kckanav/head-camera-cv/outputs/25th April 2026 - cam1 first minute sample 20s both hands.jpg

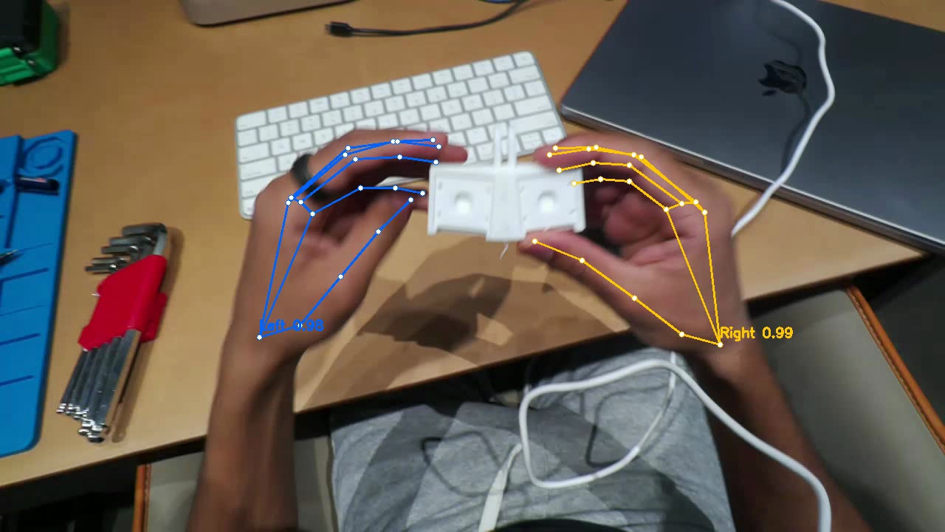
outputs/25th April 2026 - cam1 first minute sample 20s both hands.jpg
