kckanav/head-camera-cv/outputs/25th April 2026 - cam1 hands sample frame.jpg

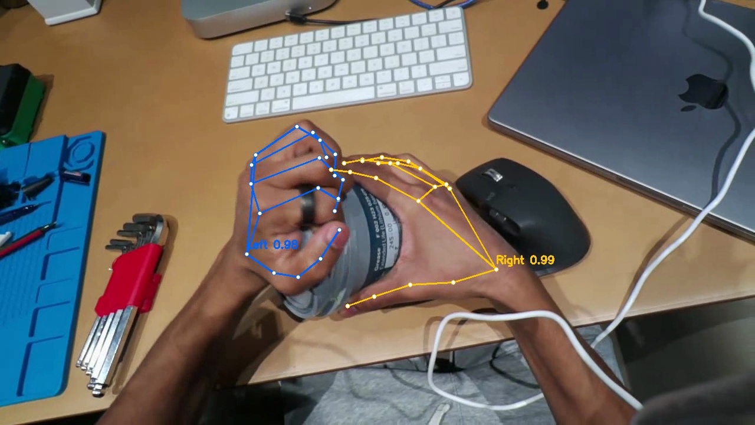
outputs/25th April 2026 - cam1 hands sample frame.jpg
