kckanav/head-camera-cv/outputs/25th April 2026 - stitched panorama sample.jpg

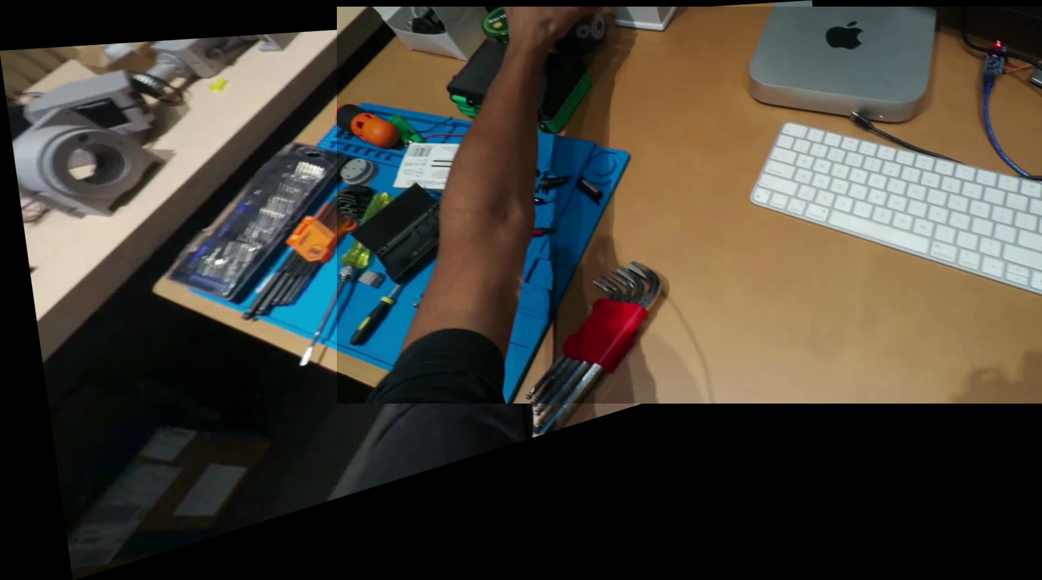
outputs/25th April 2026 - stitched panorama sample.jpg
