kckanav/head-camera-cv/outputs/27th April 2026 - rectified pair sanity.jpg

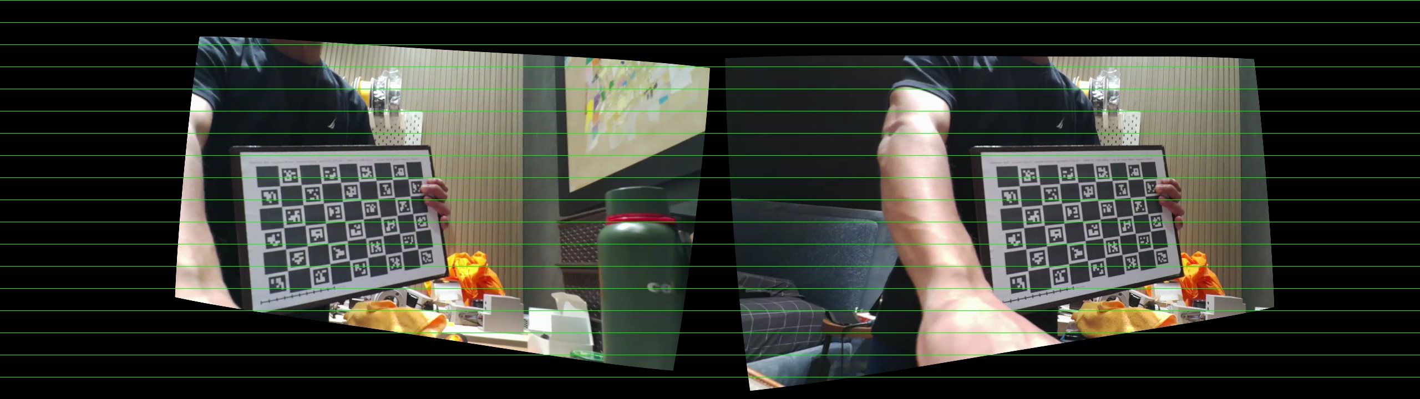
outputs/27th April 2026 - rectified pair sanity.jpg
