kckanav/head-camera-cv/outputs/27th April 2026 - stereo hand 3d trajectory.png

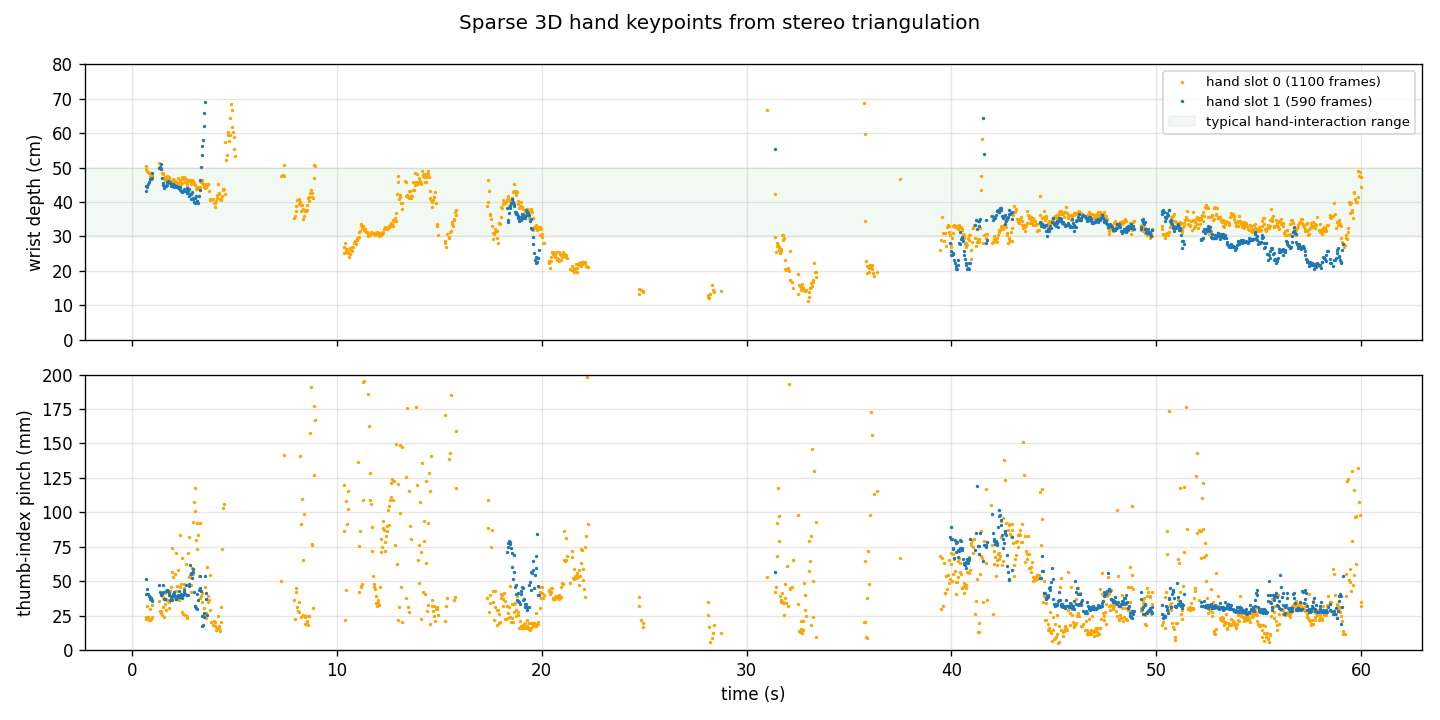
outputs/27th April 2026 - stereo hand 3d trajectory.png
