kckanav/head-camera-cv/outputs/27th April 2026 - wilor 60s perf trace.png

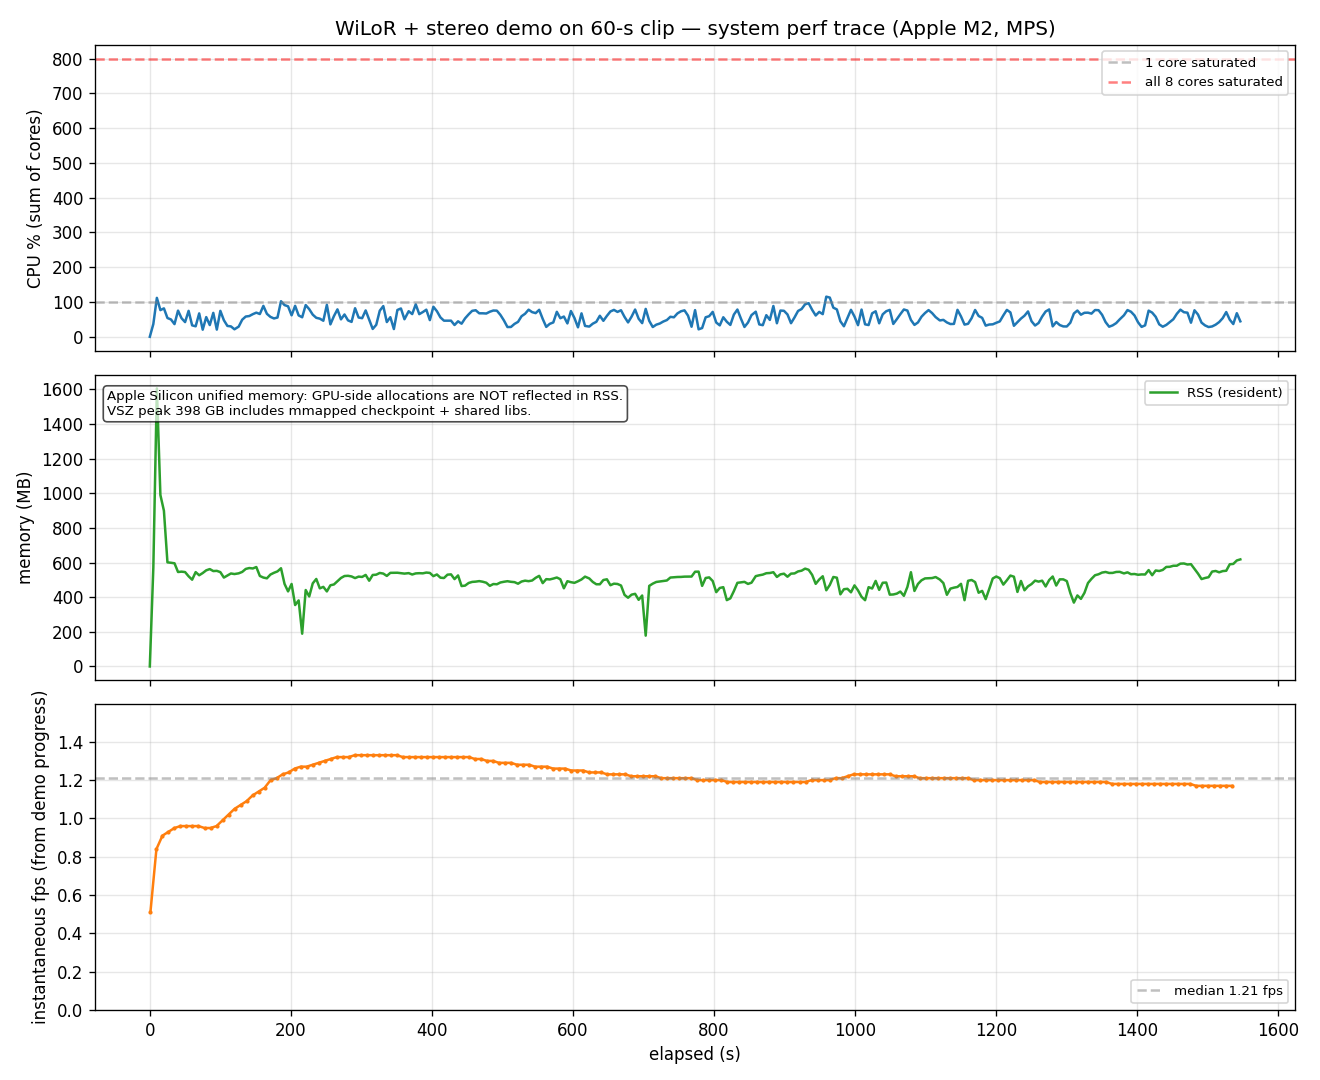
outputs/27th April 2026 - wilor 60s perf trace.png
