kckanav/head-camera-cv/outputs/27th April 2026 wide - rectified pair sanity.jpg

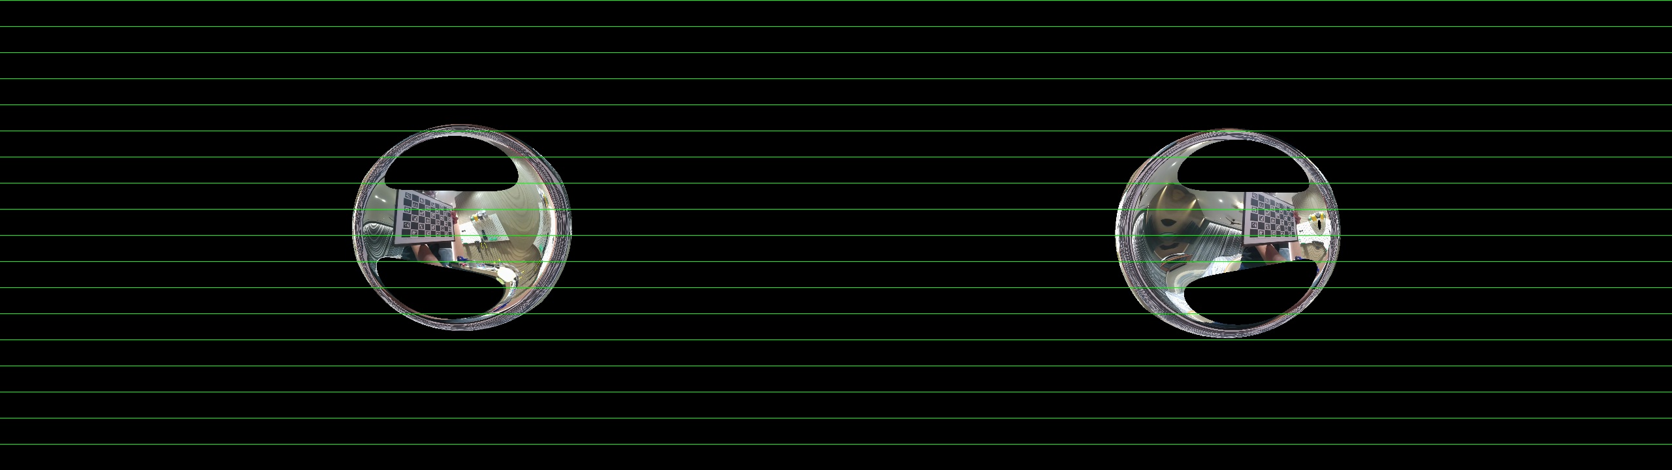
outputs/27th April 2026 wide - rectified pair sanity.jpg
