kckanav/head-camera-cv/outputs/30th April 2026 - phase4 inspection [20260430 manipulation].png

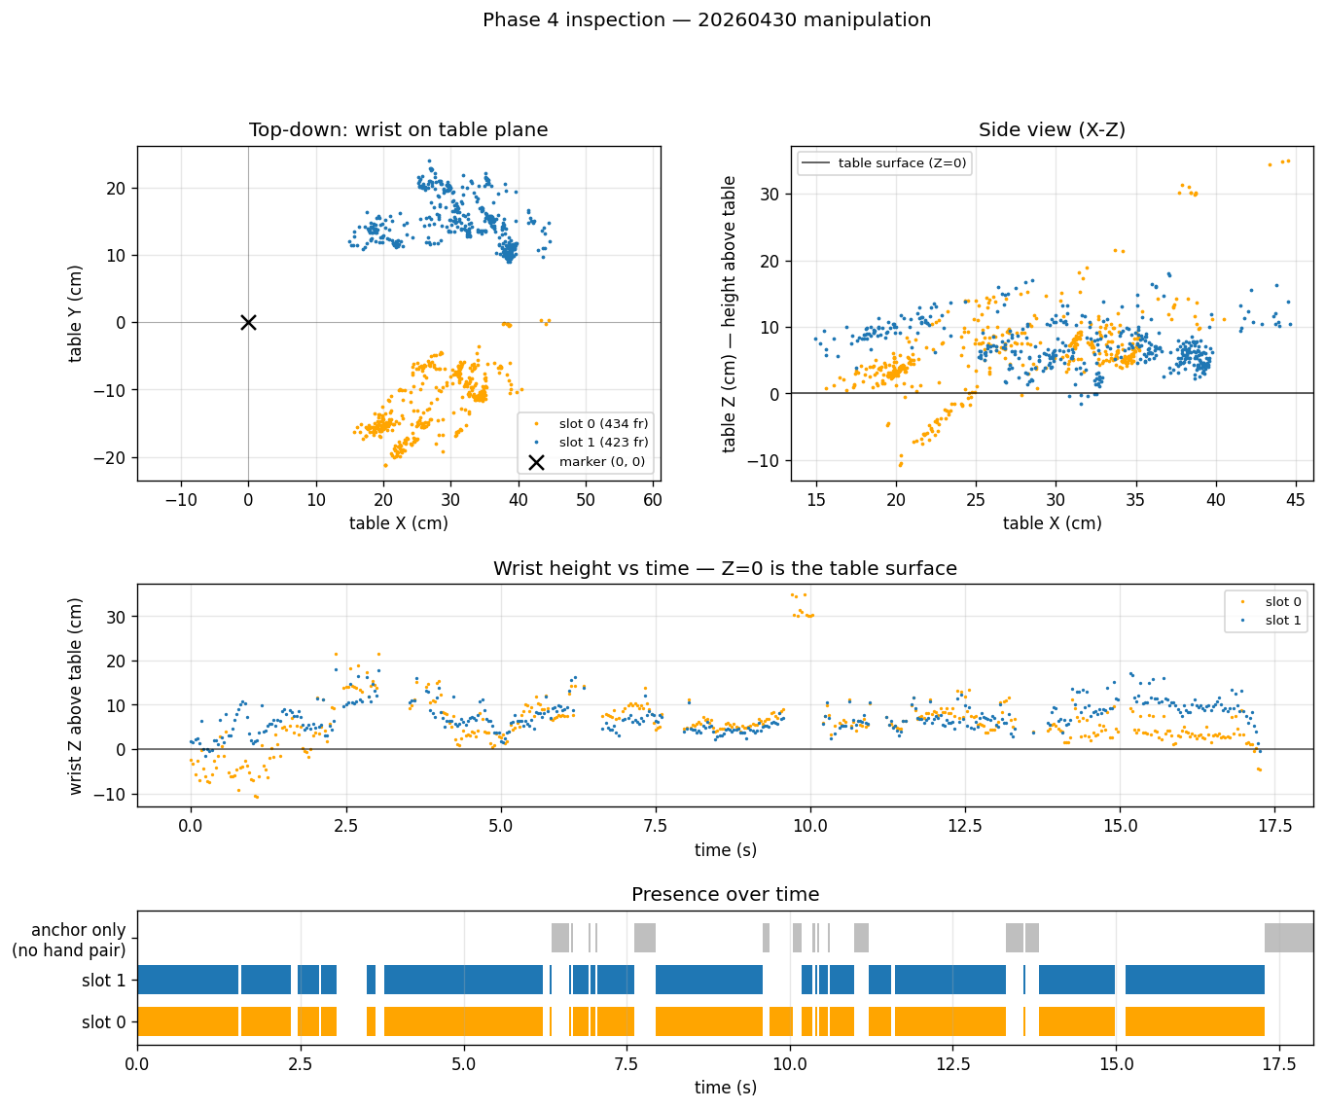
outputs/30th April 2026 - phase4 inspection [20260430 manipulation].png
