kckanav/head-camera-cv/outputs/30th April 2026 - phase4 inspection [20260430 protocol-A].png

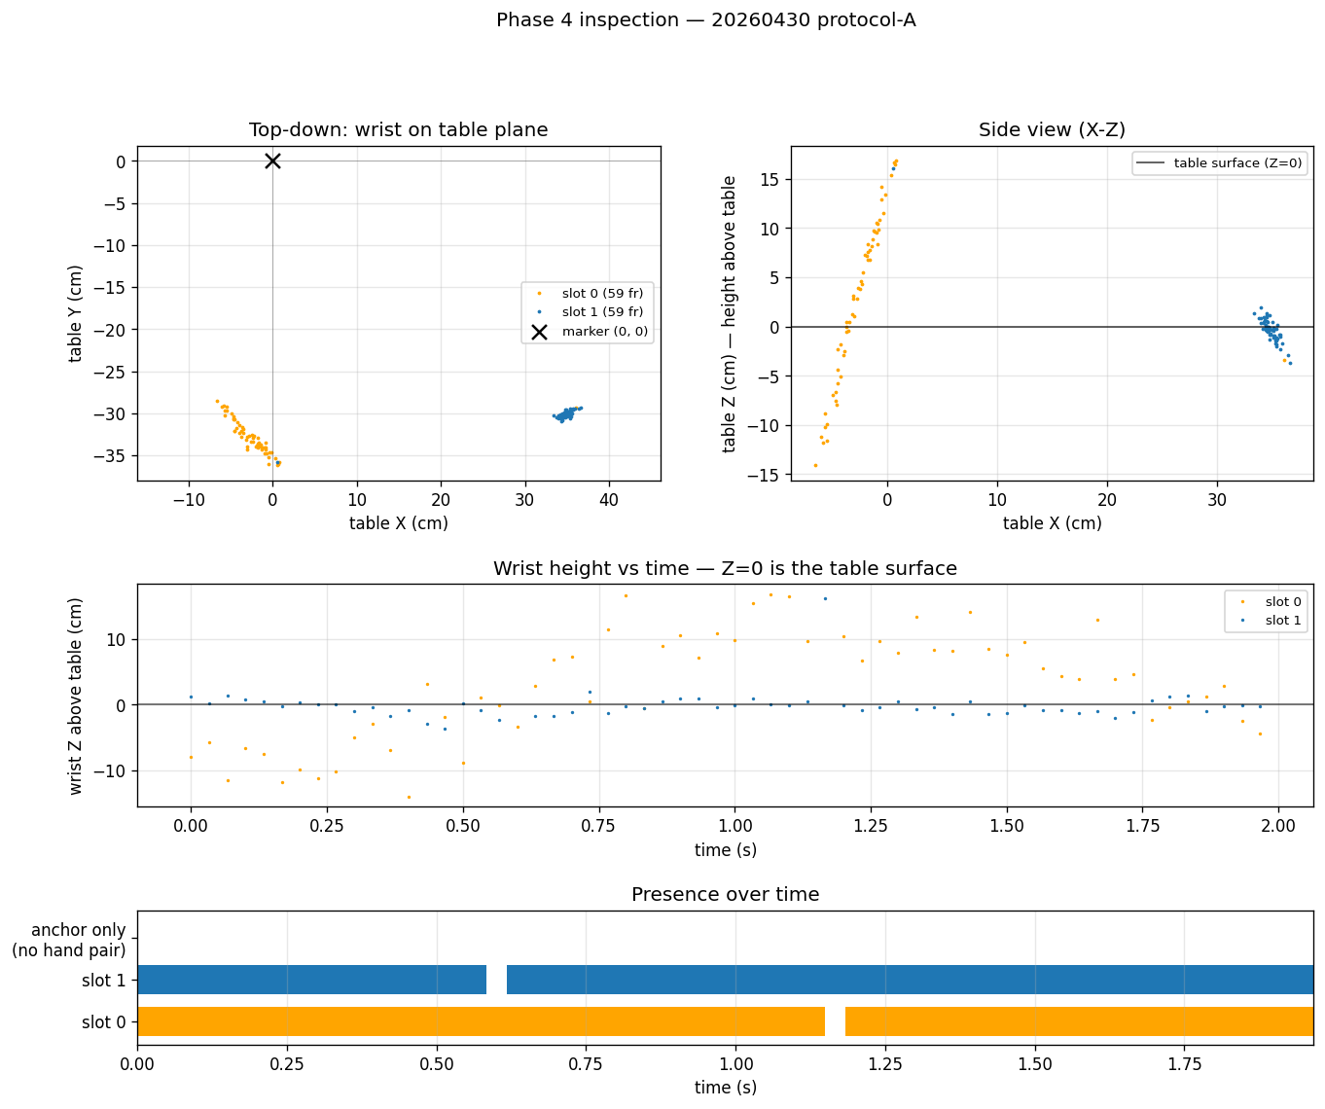
outputs/30th April 2026 - phase4 inspection [20260430 protocol-A].png
