kckanav/head-camera-cv/outputs/30th April 2026 wide - rectified pair sanity.jpg

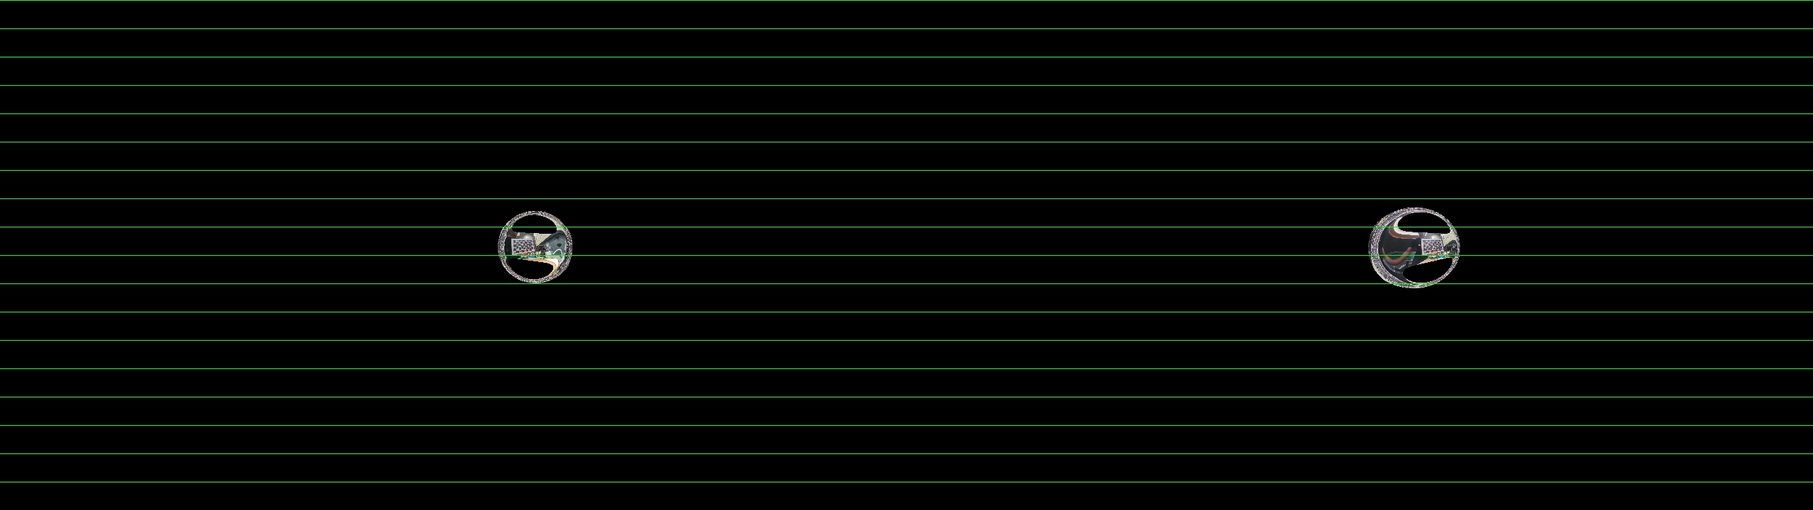
outputs/30th April 2026 wide - rectified pair sanity.jpg
