kckanav/head-camera-cv/outputs/30th April 2026 - mesh sequence [20260430 manipulation]/mesh_0003.obj

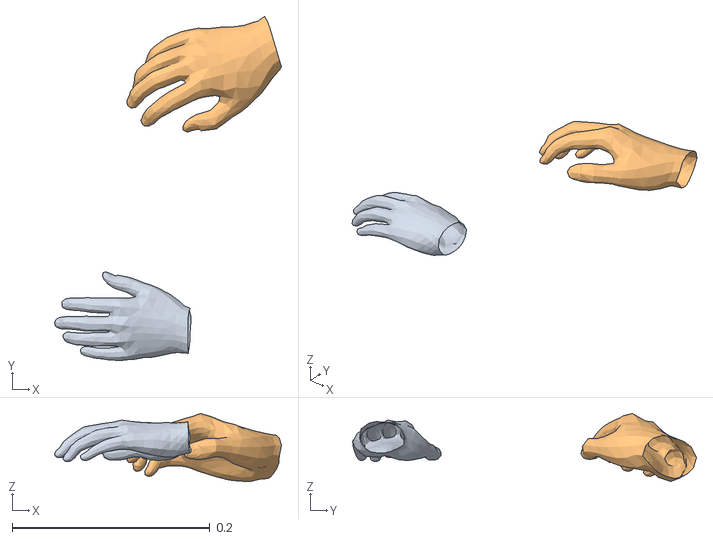
[picture p33: CAD file, 2026-04-30]
outputs/30th April 2026 - mesh sequence [20260430 manipulation]/mesh_0003.obj
0.229 x 0.348 x 0.0687
hand_slot0
hand_slot1
