kckanav/head-camera-cv/outputs/30th April 2026 - mesh sequence [20260430 manipulation]/mesh_0487.obj

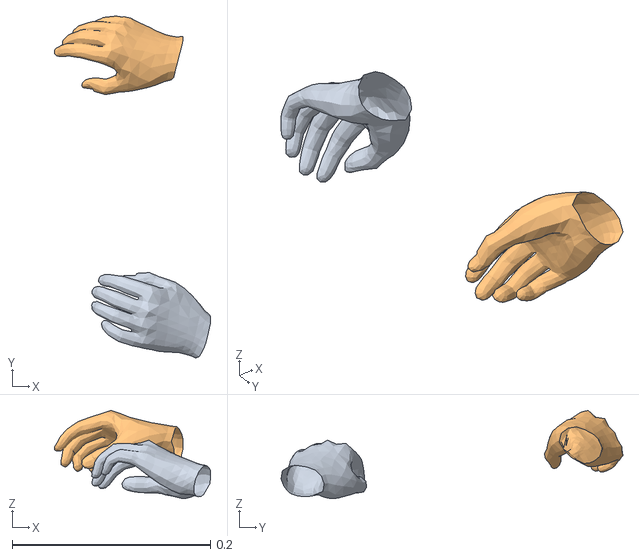
[picture p34: CAD file, 2026-04-30]
outputs/30th April 2026 - mesh sequence [20260430 manipulation]/mesh_0487.obj
0.158 x 0.345 x 0.089
hand_slot0
hand_slot1
