kckanav/head-camera-cv/outputs/30th April 2026 - mesh sequence [20260430 manipulation]/mesh_0384.obj

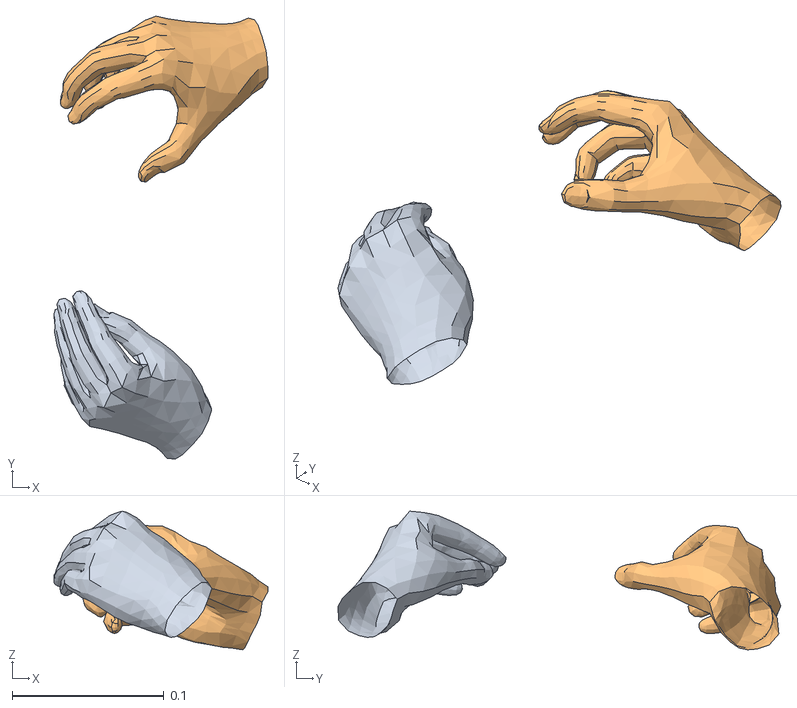
[picture p35: CAD file, 2026-04-30]
outputs/30th April 2026 - mesh sequence [20260430 manipulation]/mesh_0384.obj
0.141 x 0.292 x 0.0914
hand_slot0
hand_slot1
