kckanav/head-camera-cv/outputs/30th April 2026 - mesh sequence [20260430 manipulation]/mesh_0015.obj

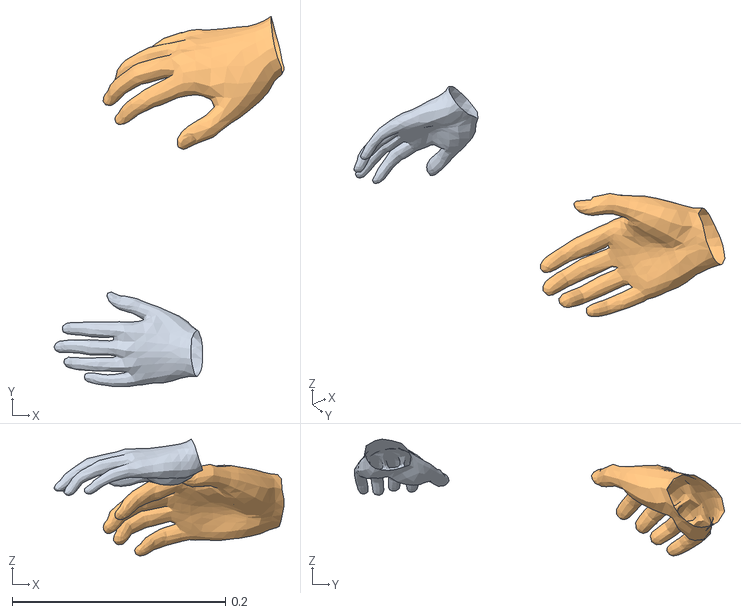
[picture p36: CAD file, 2026-04-30]
outputs/30th April 2026 - mesh sequence [20260430 manipulation]/mesh_0015.obj
0.216 x 0.347 x 0.109
hand_slot0
hand_slot1
