kckanav/head-camera-cv/outputs/30th April 2026 - mesh sequence [20260430 manipulation]/mesh_0325.obj

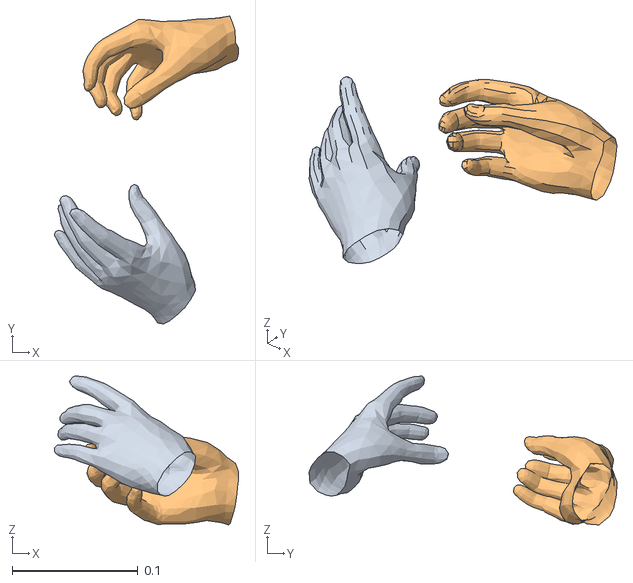
[picture p37: CAD file, 2026-04-30]
outputs/30th April 2026 - mesh sequence [20260430 manipulation]/mesh_0325.obj
0.146 x 0.245 x 0.118
hand_slot0
hand_slot1
