kckanav/head-camera-cv/outputs/30th April 2026 - mesh sequence [20260430 manipulation]/mesh_0473.obj

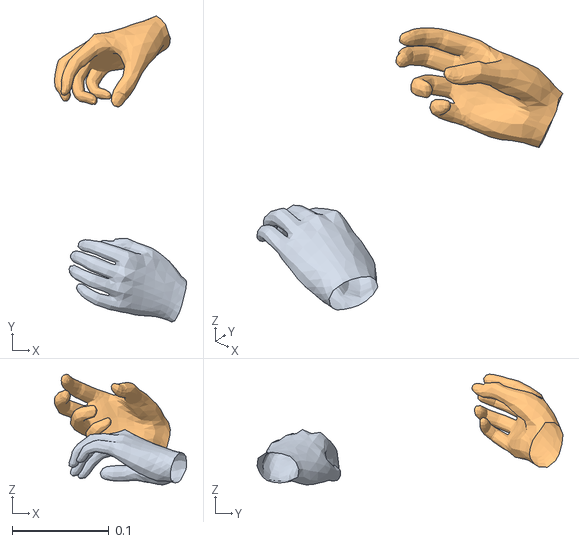
[picture p38: CAD file, 2026-04-30]
outputs/30th April 2026 - mesh sequence [20260430 manipulation]/mesh_0473.obj
0.136 x 0.316 x 0.114
hand_slot0
hand_slot1
