kckanav/head-camera-cv/outputs/30th April 2026 - mesh sequence [20260430 manipulation]/mesh_0043.obj

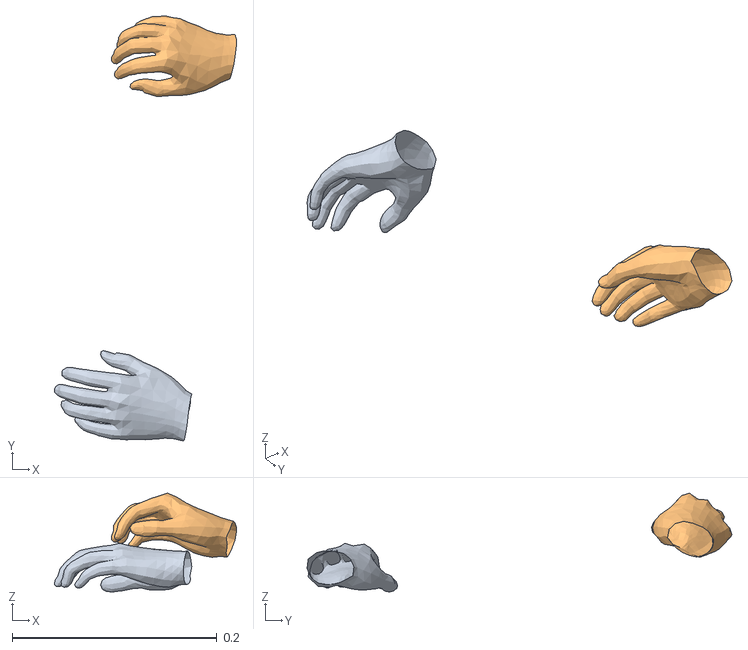
[picture p39: CAD file, 2026-04-30]
outputs/30th April 2026 - mesh sequence [20260430 manipulation]/mesh_0043.obj
0.178 x 0.415 x 0.0965
hand_slot0
hand_slot1
