kckanav/head-camera-cv/outputs/30th April 2026 - mesh sequence [20260430 manipulation]/scene.obj

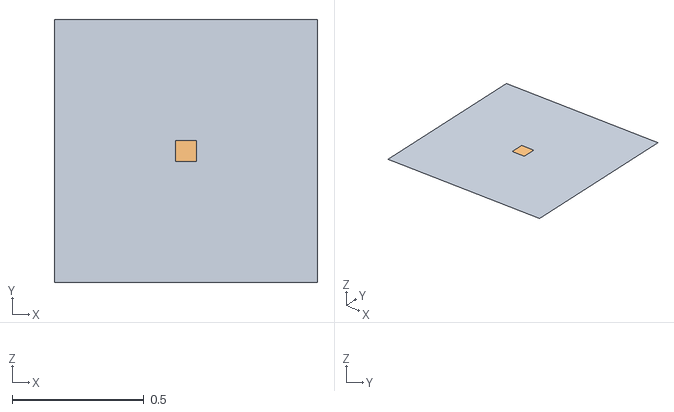
[picture p40: CAD file, 2026-04-30]
outputs/30th April 2026 - mesh sequence [20260430 manipulation]/scene.obj
1.00 x 1.00 x 0.001
table_plane
marker_outline
