kckanav/head-camera-cv/outputs/30th April 2026 - mesh sequence [20260430 manipulation]/mesh_0051.obj

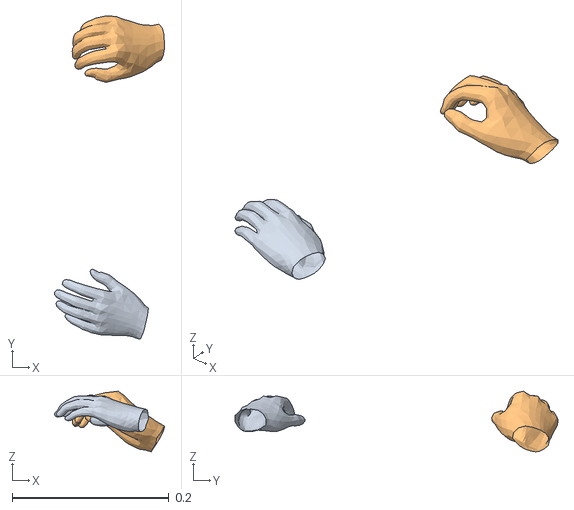
[picture p41: CAD file, 2026-04-30]
outputs/30th April 2026 - mesh sequence [20260430 manipulation]/mesh_0051.obj
0.14 x 0.413 x 0.0776
hand_slot0
hand_slot1
