kckanav/head-camera-cv/outputs/30th April 2026 - mesh sequence [20260430 manipulation]/mesh_0455.obj

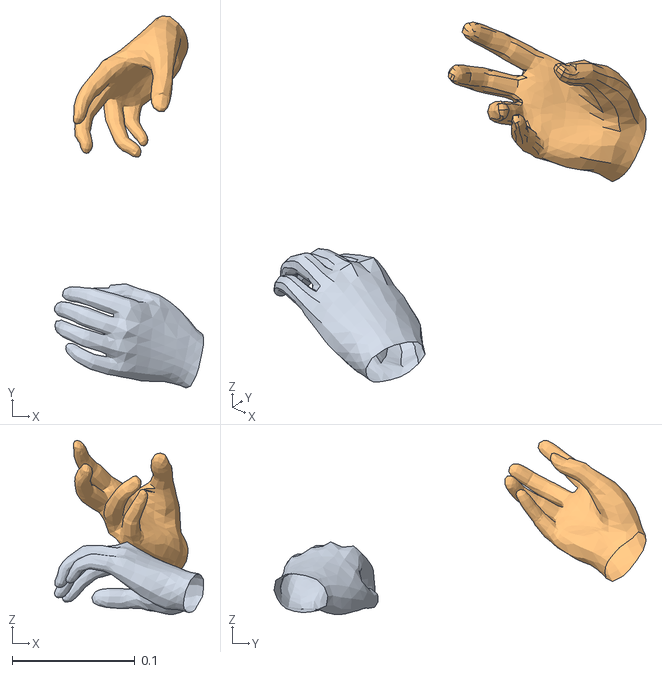
[picture p42: CAD file, 2026-04-30]
outputs/30th April 2026 - mesh sequence [20260430 manipulation]/mesh_0455.obj
0.122 x 0.303 x 0.142
hand_slot0
hand_slot1
