kckanav/head-camera-cv/outputs/30th April 2026 - mesh sequence [20260430 manipulation]/mesh_0090.obj

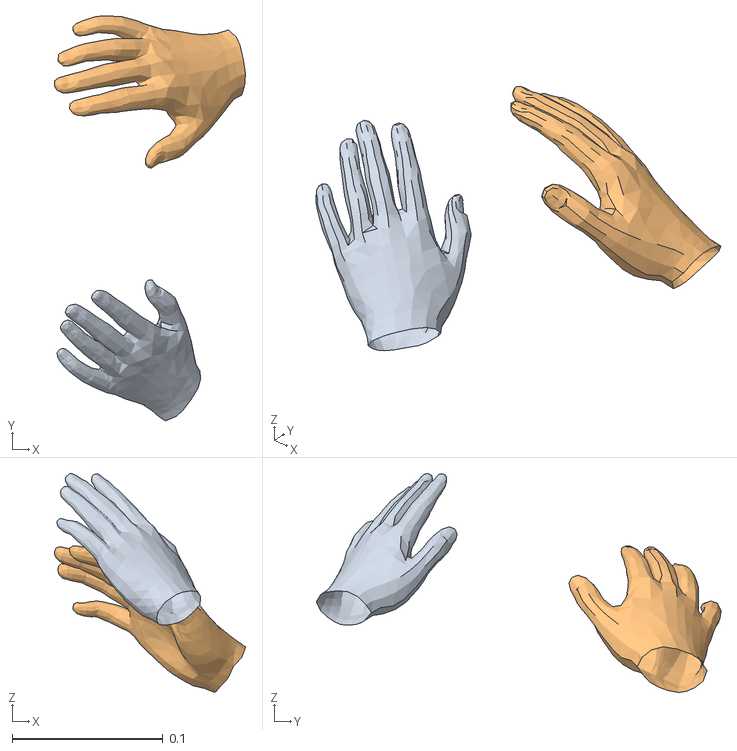
[picture p43: CAD file, 2026-04-30]
outputs/30th April 2026 - mesh sequence [20260430 manipulation]/mesh_0090.obj
0.127 x 0.268 x 0.145
hand_slot0
hand_slot1
