kckanav/head-camera-cv/outputs/30th April 2026 - mesh sequence [20260430 manipulation]/mesh_0170.obj

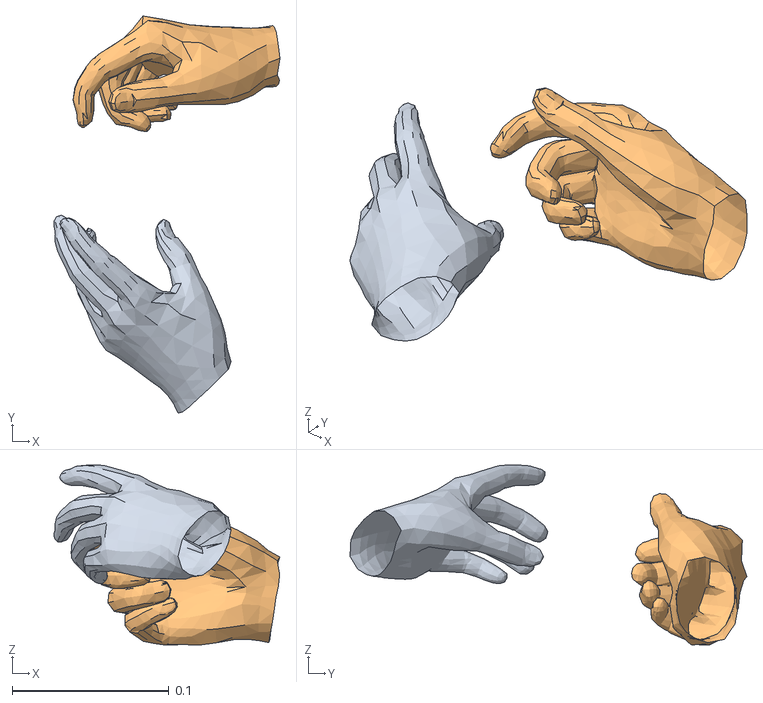
[picture p44: CAD file, 2026-04-30]
outputs/30th April 2026 - mesh sequence [20260430 manipulation]/mesh_0170.obj
0.144 x 0.253 x 0.115
hand_slot0
hand_slot1
