kckanav/head-camera-cv/outputs/30th April 2026 - mesh sequence [20260430 manipulation]/mesh_0276.obj

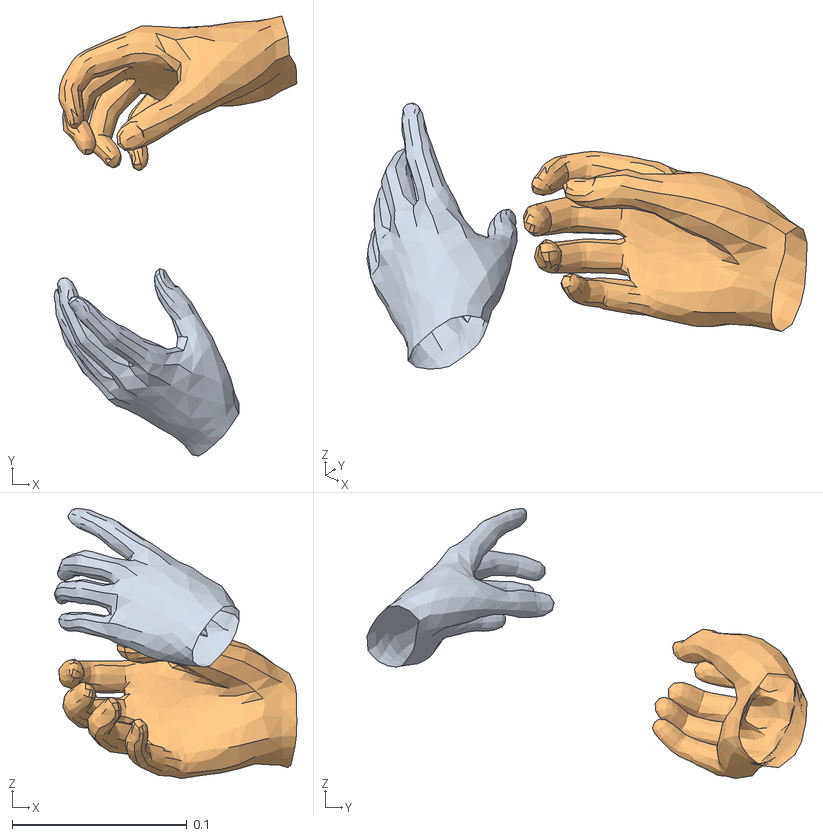
[picture p45: CAD file, 2026-04-30]
outputs/30th April 2026 - mesh sequence [20260430 manipulation]/mesh_0276.obj
0.139 x 0.252 x 0.155
hand_slot0
hand_slot1
