kckanav/head-camera-cv/outputs/30th April 2026 - mesh sequence [20260430 manipulation]/mesh_0309.obj

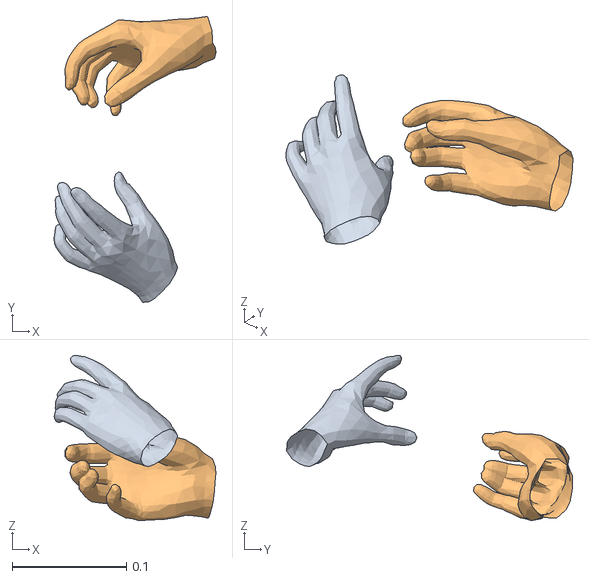
[picture p48: CAD file, 2026-04-30]
outputs/30th April 2026 - mesh sequence [20260430 manipulation]/mesh_0309.obj
0.141 x 0.25 x 0.145
hand_slot0
hand_slot1
