kckanav/head-camera-cv/outputs/30th April 2026 - mesh sequence [20260430 manipulation]/mesh_0340.obj

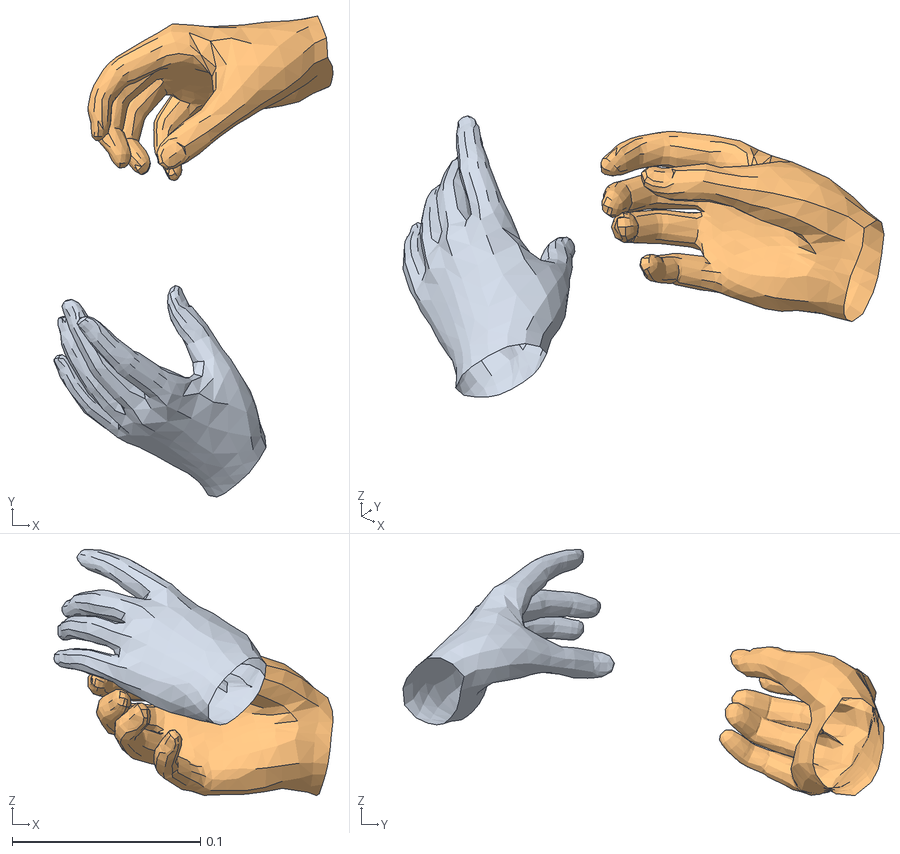
[picture p49: CAD file, 2026-04-30]
outputs/30th April 2026 - mesh sequence [20260430 manipulation]/mesh_0340.obj
0.148 x 0.256 x 0.131
hand_slot0
hand_slot1
