kckanav/head-camera-cv/outputs/30th April 2026 - mesh sequence [20260430 manipulation]/mesh_0151.obj

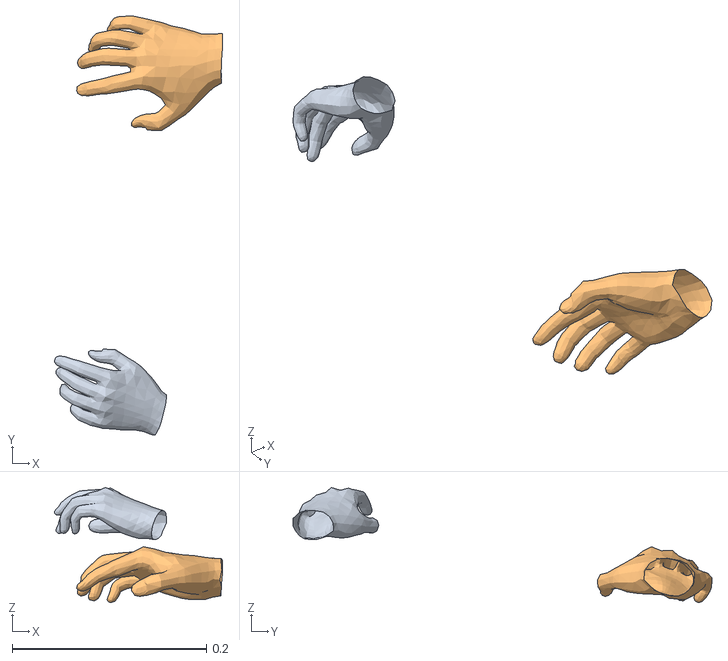
[picture p50: CAD file, 2026-04-30]
outputs/30th April 2026 - mesh sequence [20260430 manipulation]/mesh_0151.obj
0.173 x 0.432 x 0.119
hand_slot0
hand_slot1
