kckanav/head-camera-cv/outputs/30th April 2026 - mesh sequence [20260430 manipulation]/mesh_0142.obj

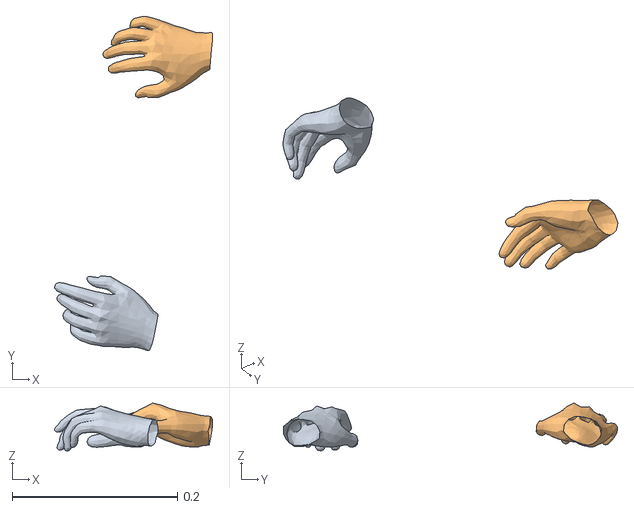
[picture p51: CAD file, 2026-04-30]
outputs/30th April 2026 - mesh sequence [20260430 manipulation]/mesh_0142.obj
0.191 x 0.405 x 0.058
hand_slot0
hand_slot1
