kckanav/head-camera-cv/outputs/30th April 2026 - mesh sequence [20260430 manipulation]/mesh_0272.obj

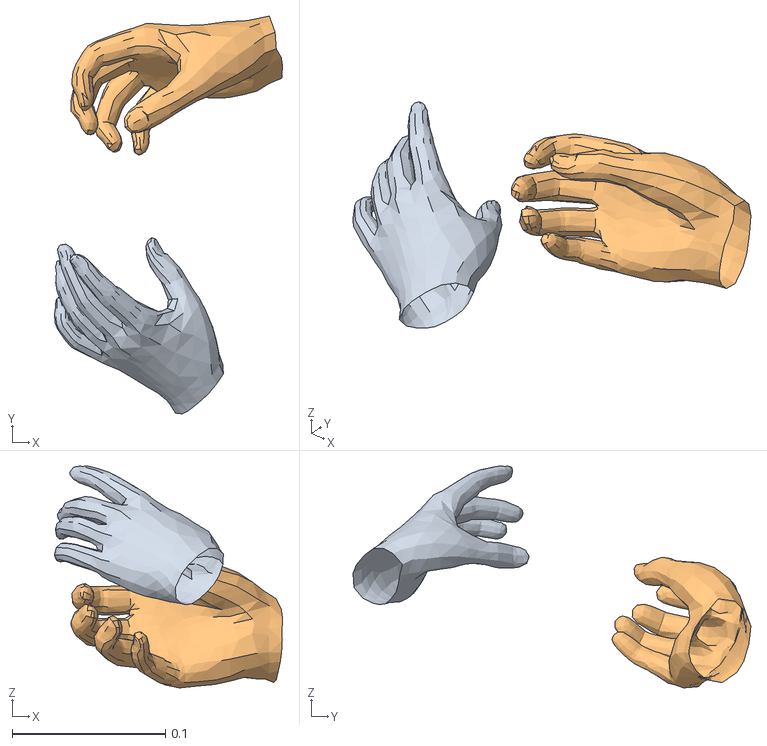
[picture p52: CAD file, 2026-04-30]
outputs/30th April 2026 - mesh sequence [20260430 manipulation]/mesh_0272.obj
0.149 x 0.26 x 0.145
hand_slot0
hand_slot1
