kckanav/head-camera-cv/outputs/30th April 2026 - mesh sequence [20260430 manipulation]/mesh_0432.obj

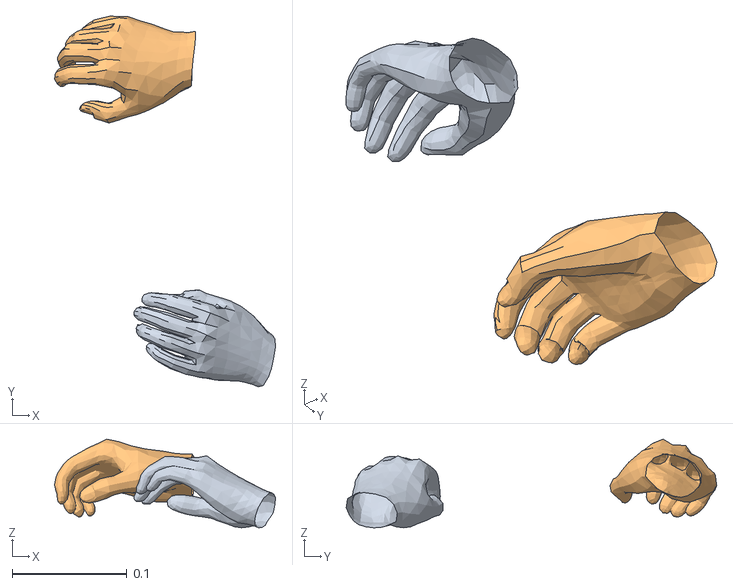
[picture p53: CAD file, 2026-04-30]
outputs/30th April 2026 - mesh sequence [20260430 manipulation]/mesh_0432.obj
0.193 x 0.323 x 0.0774
hand_slot0
hand_slot1
