kckanav/head-camera-cv/outputs/30th April 2026 - mesh sequence [20260430 manipulation]/mesh_0391.obj

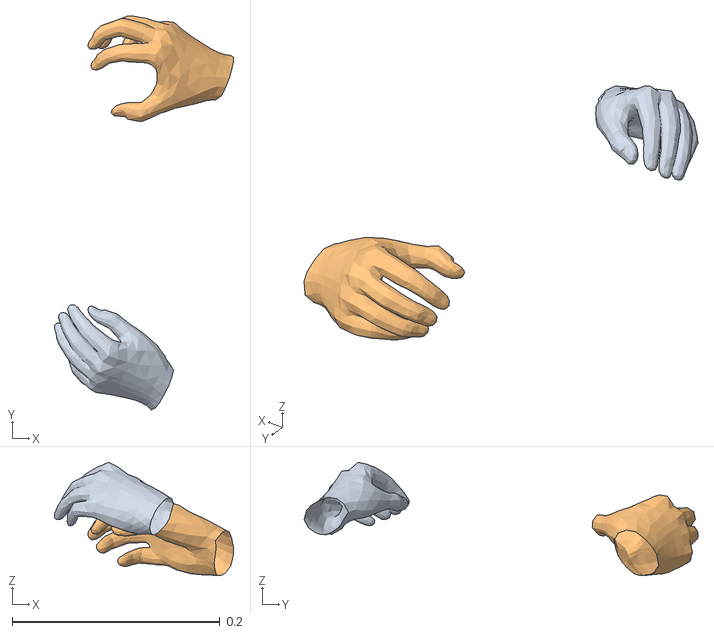
[picture p54: CAD file, 2026-04-30]
outputs/30th April 2026 - mesh sequence [20260430 manipulation]/mesh_0391.obj
0.172 x 0.379 x 0.109
hand_slot0
hand_slot1
