kckanav/head-camera-cv/outputs/30th April 2026 - mesh sequence [20260430 manipulation]/mesh_0346.obj

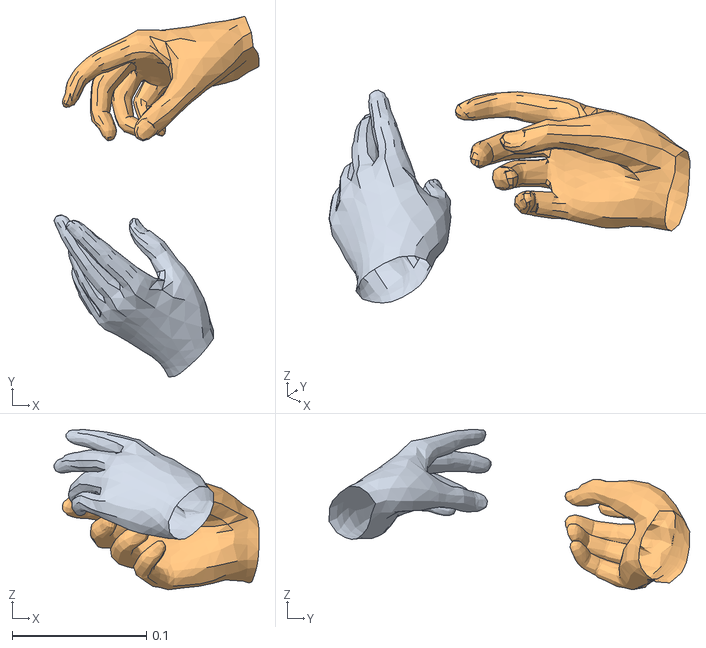
[picture p55: CAD file, 2026-04-30]
outputs/30th April 2026 - mesh sequence [20260430 manipulation]/mesh_0346.obj
0.153 x 0.269 x 0.12
hand_slot0
hand_slot1
