kckanav/head-camera-cv/outputs/30th April 2026 - mesh sequence [20260430 manipulation]/mesh_0386.obj

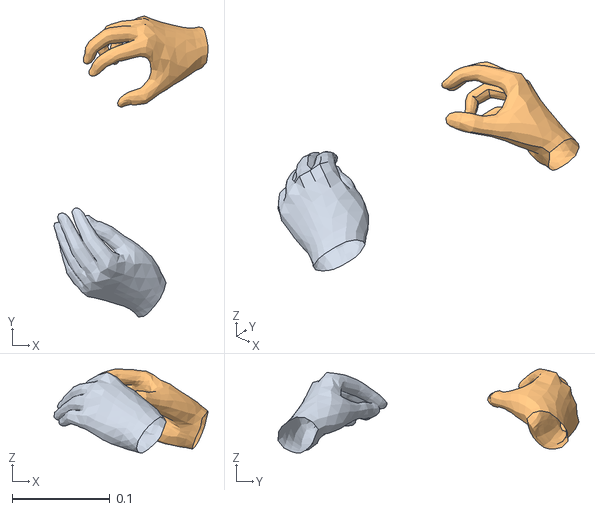
[picture p56: CAD file, 2026-04-30]
outputs/30th April 2026 - mesh sequence [20260430 manipulation]/mesh_0386.obj
0.157 x 0.308 x 0.0857
hand_slot0
hand_slot1
