kckanav/head-camera-cv/outputs/30th April 2026 - mesh sequence [20260430 manipulation]/mesh_0475.obj

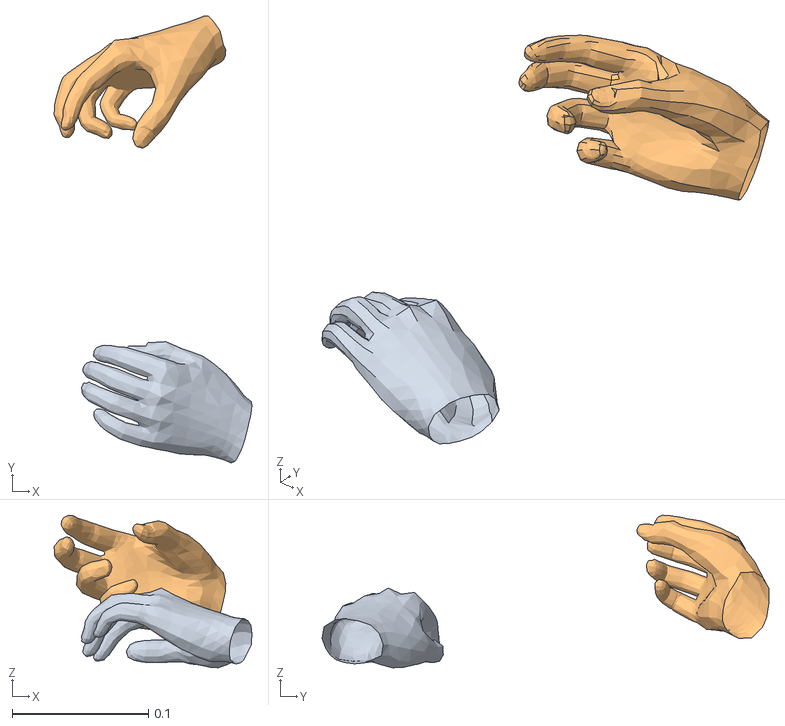
[picture p57: CAD file, 2026-04-30]
outputs/30th April 2026 - mesh sequence [20260430 manipulation]/mesh_0475.obj
0.145 x 0.328 x 0.112
hand_slot0
hand_slot1
