kckanav/head-camera-cv/outputs/30th April 2026 - mesh sequence [20260430 manipulation]/mesh_0253.obj

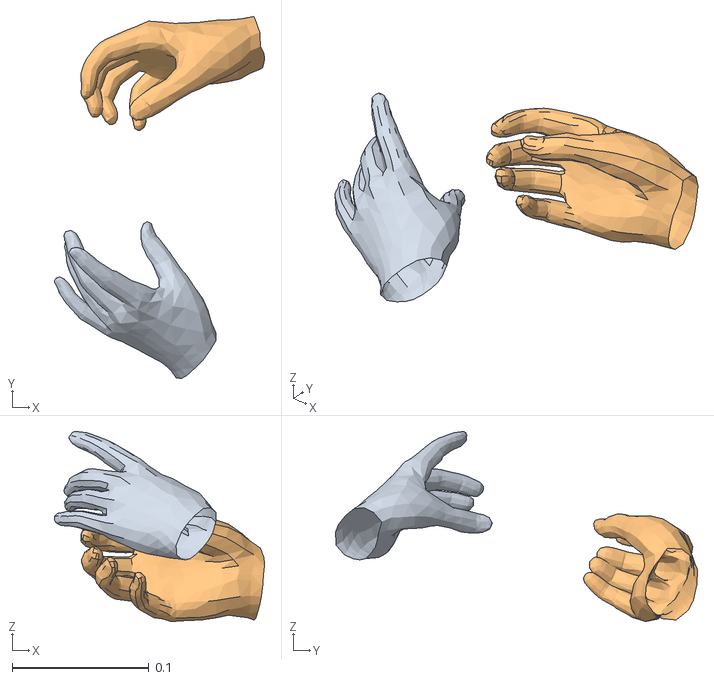
[picture p58: CAD file, 2026-04-30]
outputs/30th April 2026 - mesh sequence [20260430 manipulation]/mesh_0253.obj
0.153 x 0.265 x 0.139
hand_slot0
hand_slot1
