kckanav/head-camera-cv/outputs/30th April 2026 - mesh sequence [20260430 manipulation]/mesh_0150.obj

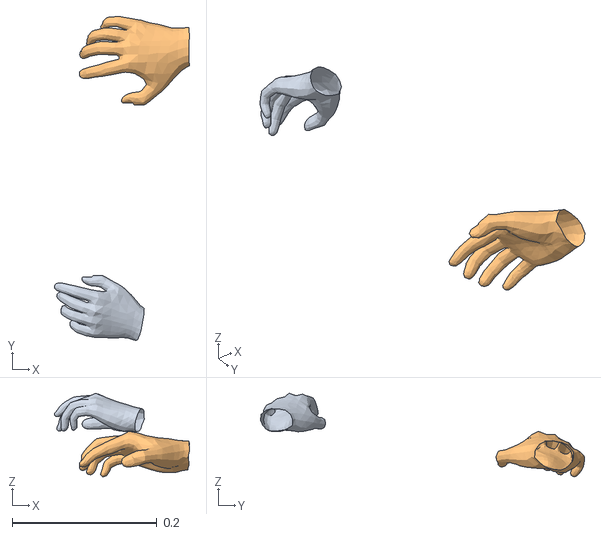
[picture p59: CAD file, 2026-04-30]
outputs/30th April 2026 - mesh sequence [20260430 manipulation]/mesh_0150.obj
0.187 x 0.447 x 0.115
hand_slot0
hand_slot1
