kckanav/head-camera-cv/outputs/30th April 2026 - mesh sequence [20260430 manipulation]/mesh_0456.obj

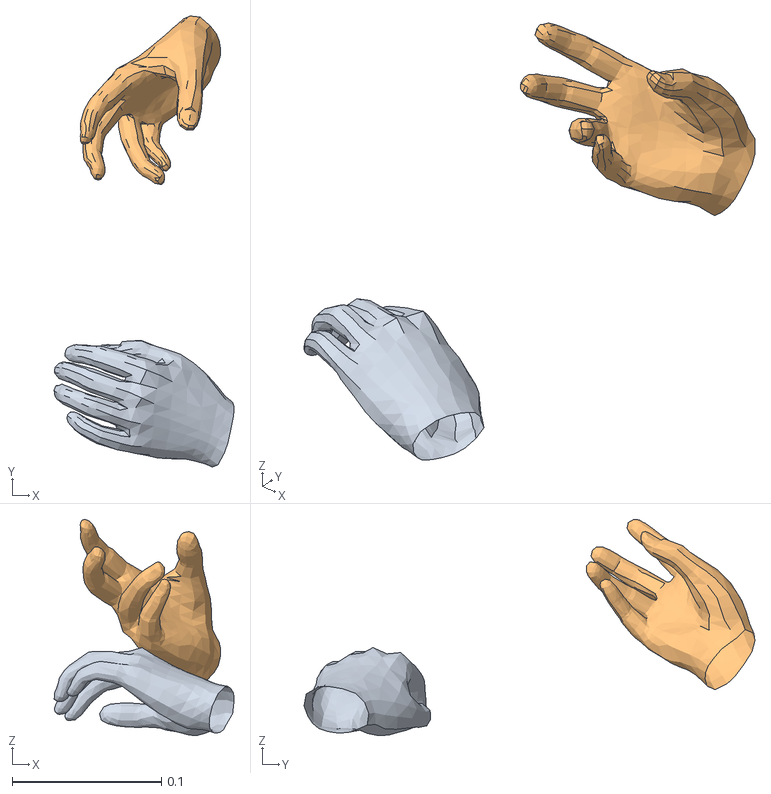
[picture p61: CAD file, 2026-04-30]
outputs/30th April 2026 - mesh sequence [20260430 manipulation]/mesh_0456.obj
0.121 x 0.302 x 0.145
hand_slot0
hand_slot1
