kckanav/head-camera-cv/outputs/30th April 2026 - mesh sequence [20260430 manipulation]/mesh_0360.obj

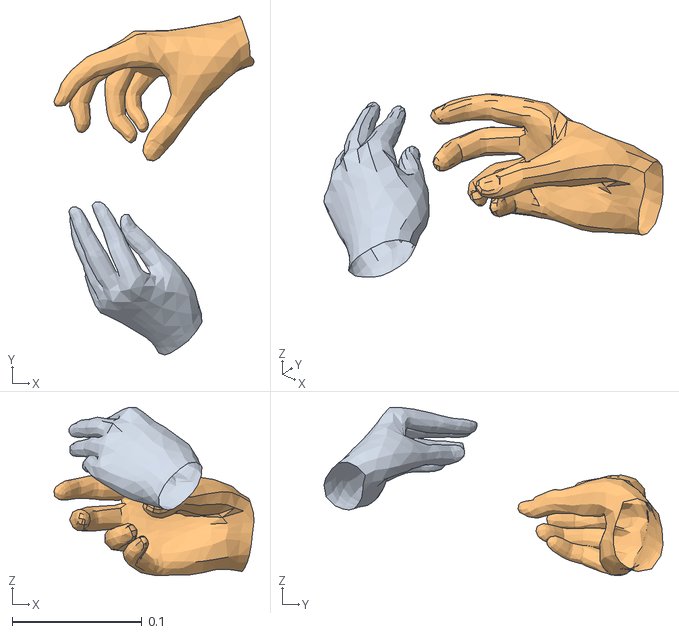
[picture p62: CAD file, 2026-04-30]
outputs/30th April 2026 - mesh sequence [20260430 manipulation]/mesh_0360.obj
0.154 x 0.262 x 0.13
hand_slot0
hand_slot1
