kckanav/head-camera-cv/outputs/30th April 2026 - mesh sequence [20260430 manipulation]/mesh_0362.obj

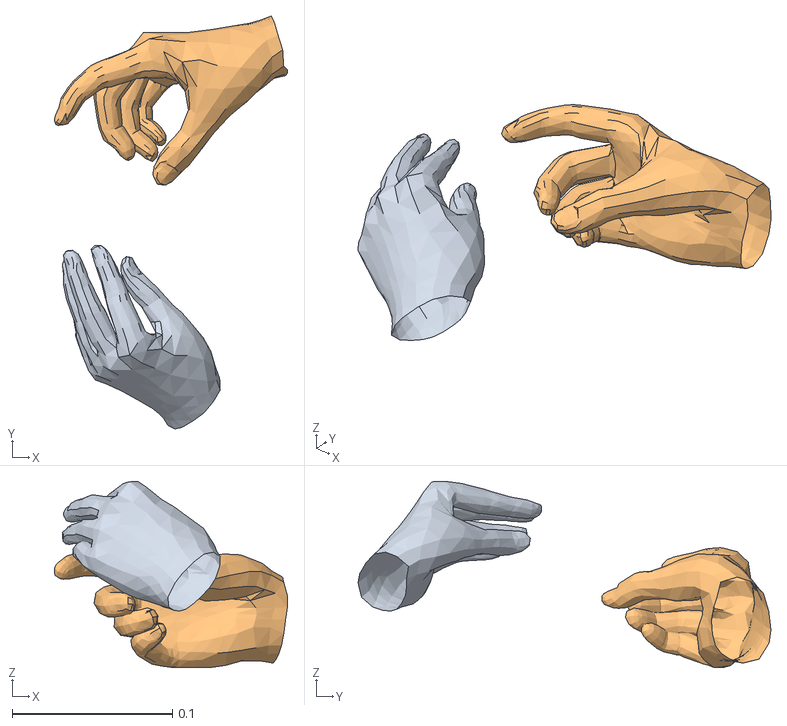
[picture p63: CAD file, 2026-04-30]
outputs/30th April 2026 - mesh sequence [20260430 manipulation]/mesh_0362.obj
0.145 x 0.258 x 0.116
hand_slot0
hand_slot1
