kckanav/head-camera-cv/outputs/30th April 2026 - mesh sequence [20260430 manipulation]/mesh_0004.obj

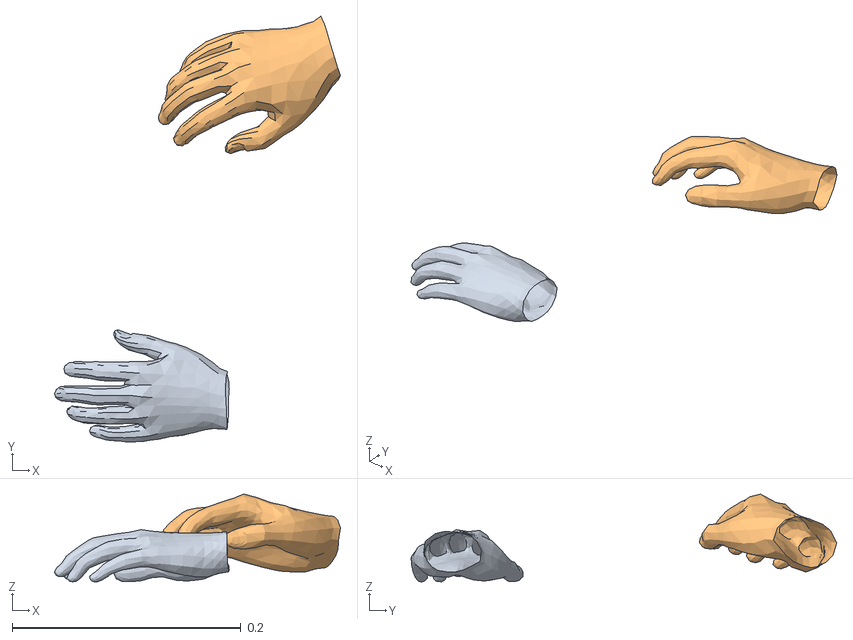
[picture p64: CAD file, 2026-04-30]
outputs/30th April 2026 - mesh sequence [20260430 manipulation]/mesh_0004.obj
0.25 x 0.372 x 0.0768
hand_slot0
hand_slot1
