kckanav/head-camera-cv/outputs/30th April 2026 - mesh sequence [20260430 manipulation]/mesh_0075.obj

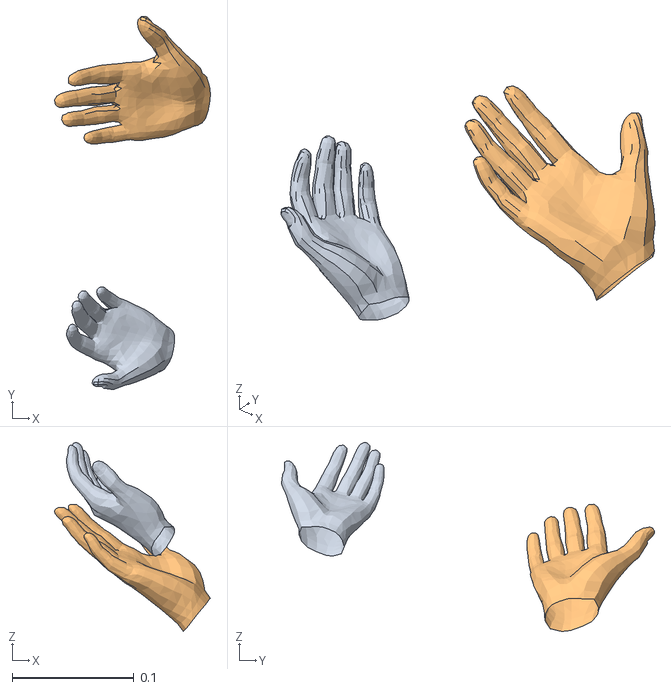
[picture p65: CAD file, 2026-04-30]
outputs/30th April 2026 - mesh sequence [20260430 manipulation]/mesh_0075.obj
0.128 x 0.307 x 0.155
hand_slot0
hand_slot1
