kckanav/head-camera-cv/outputs/30th April 2026 - mesh sequence [20260430 manipulation]/mesh_0134.obj

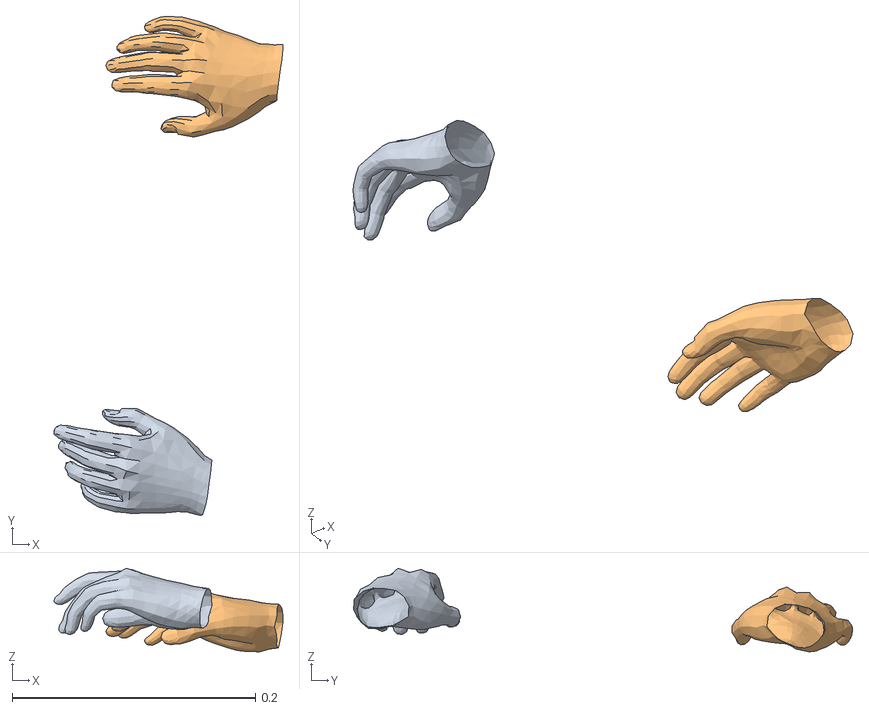
[picture p67: CAD file, 2026-04-30]
outputs/30th April 2026 - mesh sequence [20260430 manipulation]/mesh_0134.obj
0.188 x 0.41 x 0.0687
hand_slot0
hand_slot1
