kckanav/head-camera-cv/outputs/30th April 2026 - mesh sequence [20260430 manipulation]/mesh_0248.obj

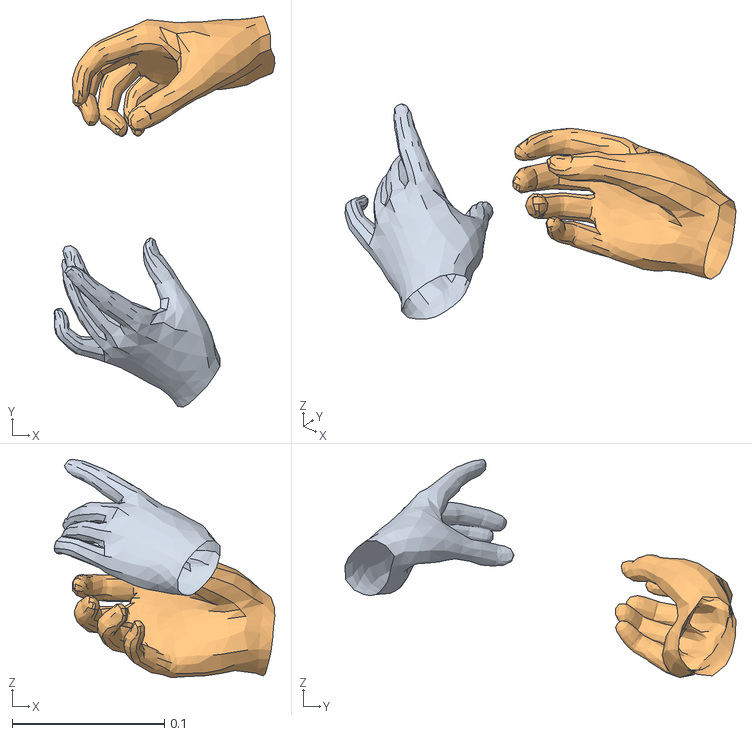
[picture p68: CAD file, 2026-04-30]
outputs/30th April 2026 - mesh sequence [20260430 manipulation]/mesh_0248.obj
0.145 x 0.257 x 0.143
hand_slot0
hand_slot1
