kckanav/head-camera-cv/outputs/30th April 2026 - mesh sequence [20260430 manipulation]/mesh_0161.obj

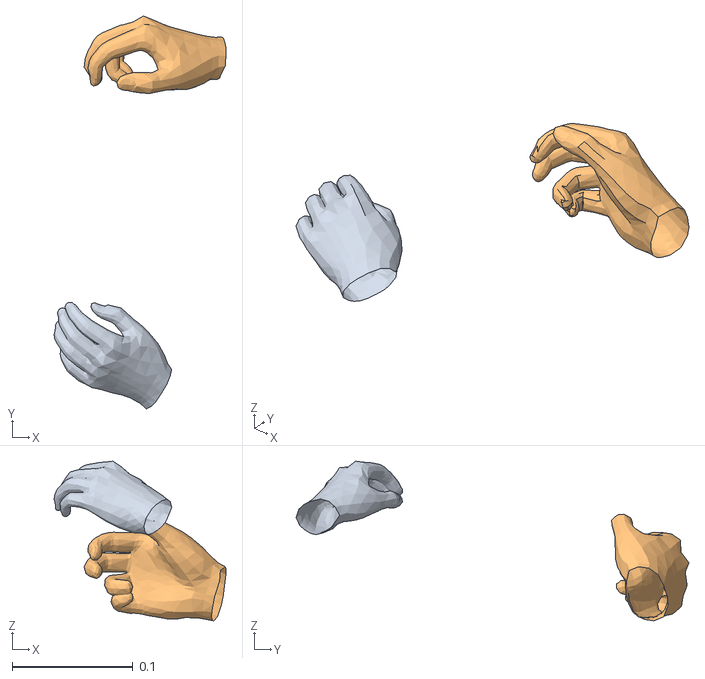
[picture p69: CAD file, 2026-04-30]
outputs/30th April 2026 - mesh sequence [20260430 manipulation]/mesh_0161.obj
0.142 x 0.325 x 0.132
hand_slot0
hand_slot1
