kckanav/head-camera-cv/outputs/30th April 2026 - mesh sequence [20260430 manipulation]/mesh_0223.obj

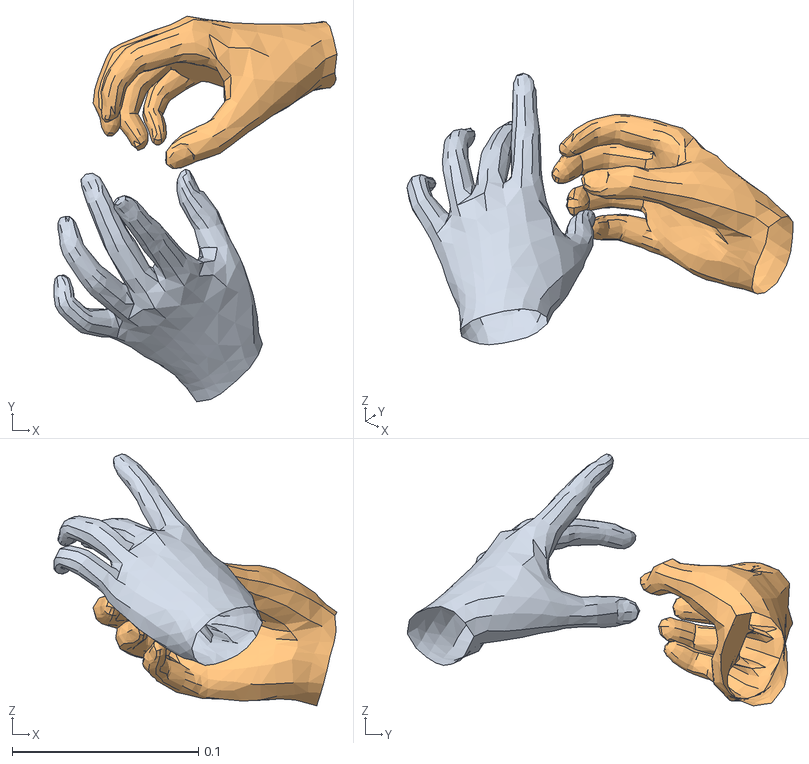
[picture p70: CAD file, 2026-04-30]
outputs/30th April 2026 - mesh sequence [20260430 manipulation]/mesh_0223.obj
0.152 x 0.207 x 0.135
hand_slot0
hand_slot1
