kckanav/head-camera-cv/outputs/30th April 2026 - mesh sequence [20260430 manipulation]/mesh_0449.obj

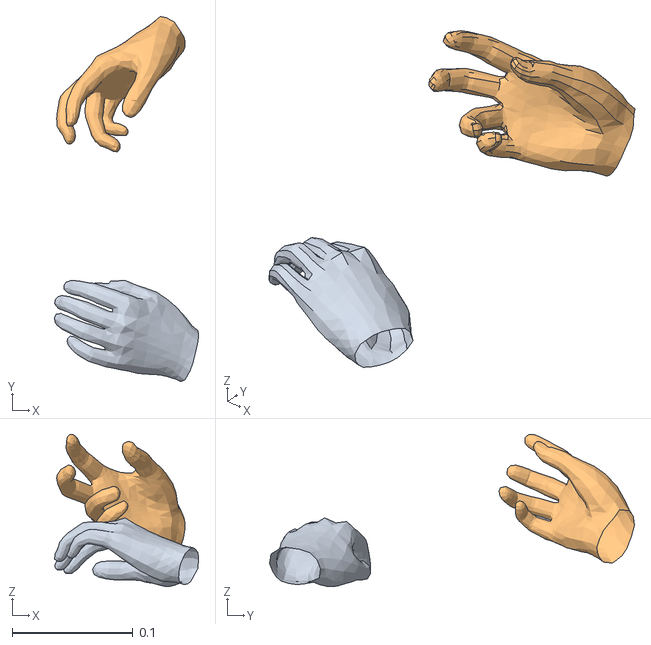
[picture p72: CAD file, 2026-04-30]
outputs/30th April 2026 - mesh sequence [20260430 manipulation]/mesh_0449.obj
0.12 x 0.303 x 0.126
hand_slot0
hand_slot1
