kckanav/head-camera-cv/outputs/30th April 2026 - mesh sequence [20260430 manipulation]/mesh_0448.obj

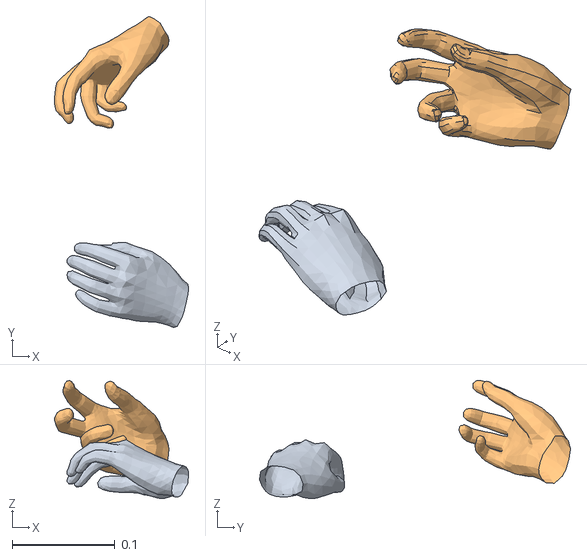
[picture p73: CAD file, 2026-04-30]
outputs/30th April 2026 - mesh sequence [20260430 manipulation]/mesh_0448.obj
0.131 x 0.304 x 0.115
hand_slot0
hand_slot1
