kckanav/head-camera-cv/outputs/30th April 2026 - mesh sequence [20260430 manipulation]/mesh_0013.obj

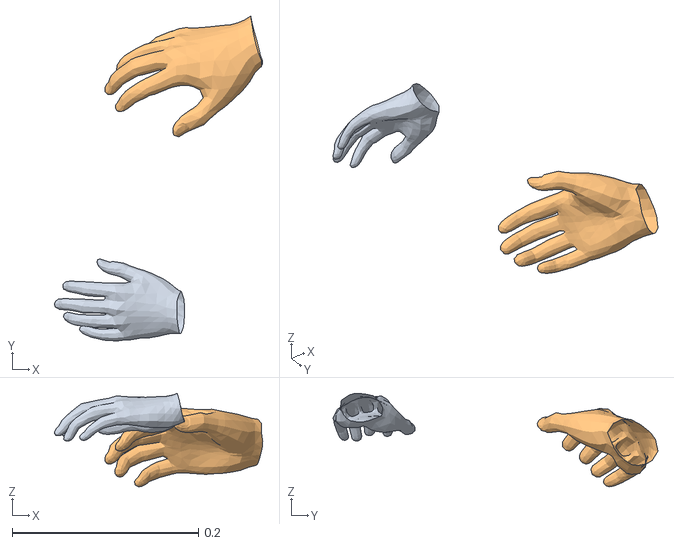
[picture p74: CAD file, 2026-04-30]
outputs/30th April 2026 - mesh sequence [20260430 manipulation]/mesh_0013.obj
0.224 x 0.349 x 0.1
hand_slot0
hand_slot1
