kckanav/head-camera-cv/outputs/30th April 2026 - mesh sequence [20260430 manipulation]/mesh_0287.obj

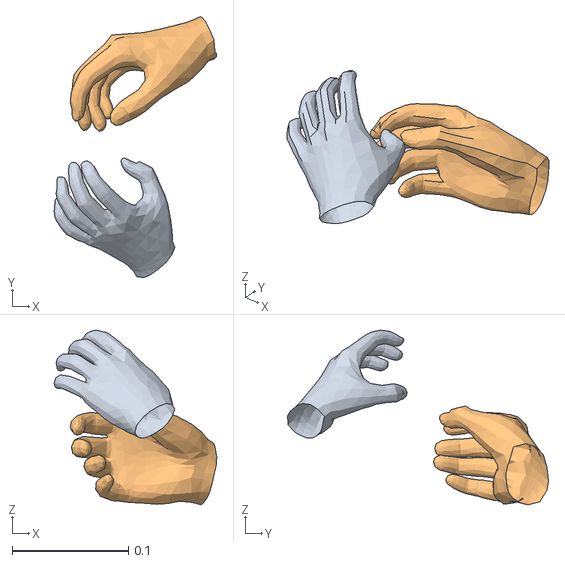
[picture p75: CAD file, 2026-04-30]
outputs/30th April 2026 - mesh sequence [20260430 manipulation]/mesh_0287.obj
0.14 x 0.225 x 0.15
hand_slot0
hand_slot1
