kckanav/head-camera-cv/outputs/30th April 2026 - mesh sequence [20260430 manipulation]/mesh_0077.obj

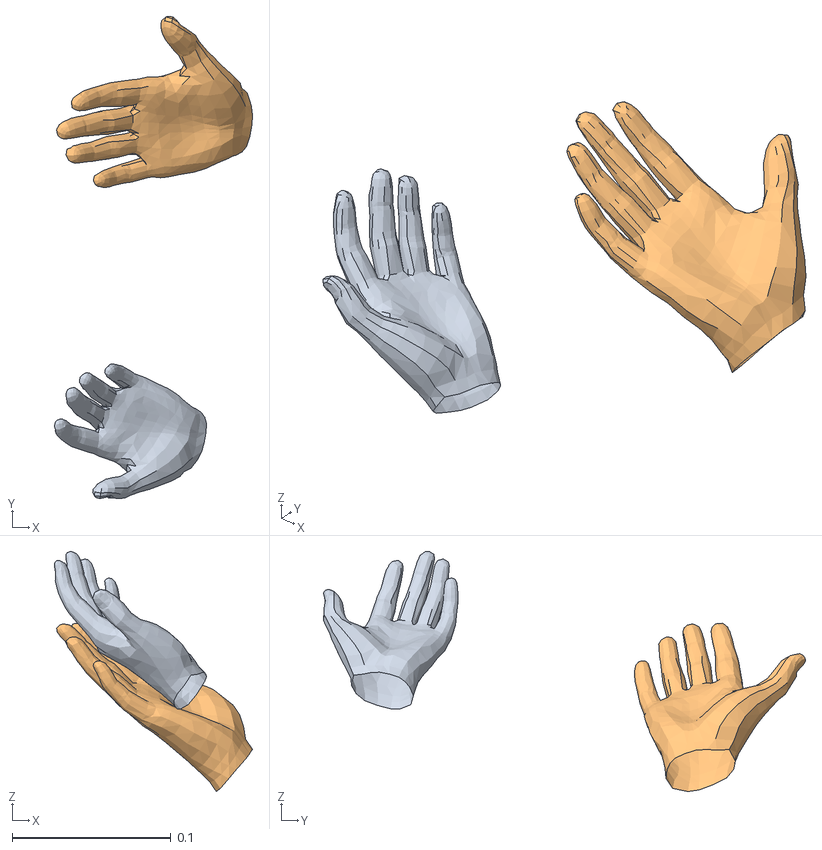
[picture p76: CAD file, 2026-04-30]
outputs/30th April 2026 - mesh sequence [20260430 manipulation]/mesh_0077.obj
0.125 x 0.304 x 0.151
hand_slot0
hand_slot1
