kckanav/head-camera-cv/outputs/30th April 2026 - mesh sequence [20260430 manipulation]/mesh_0418.obj

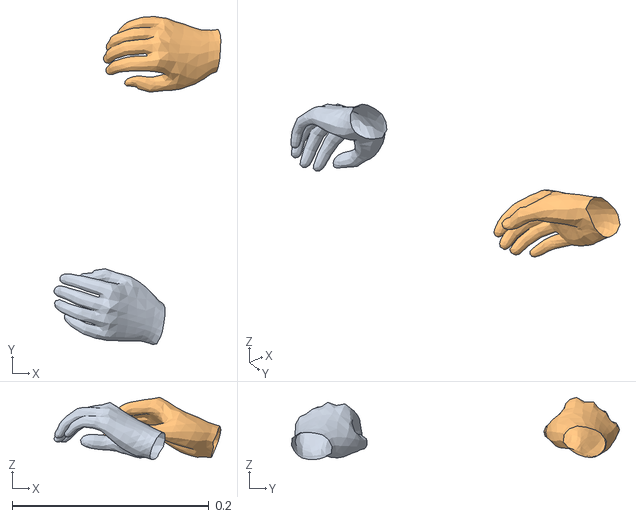
[picture p77: CAD file, 2026-04-30]
outputs/30th April 2026 - mesh sequence [20260430 manipulation]/mesh_0418.obj
0.17 x 0.334 x 0.0634
hand_slot0
hand_slot1
