kckanav/head-camera-cv/outputs/30th April 2026 - mesh sequence [20260430 manipulation]/mesh_0181.obj

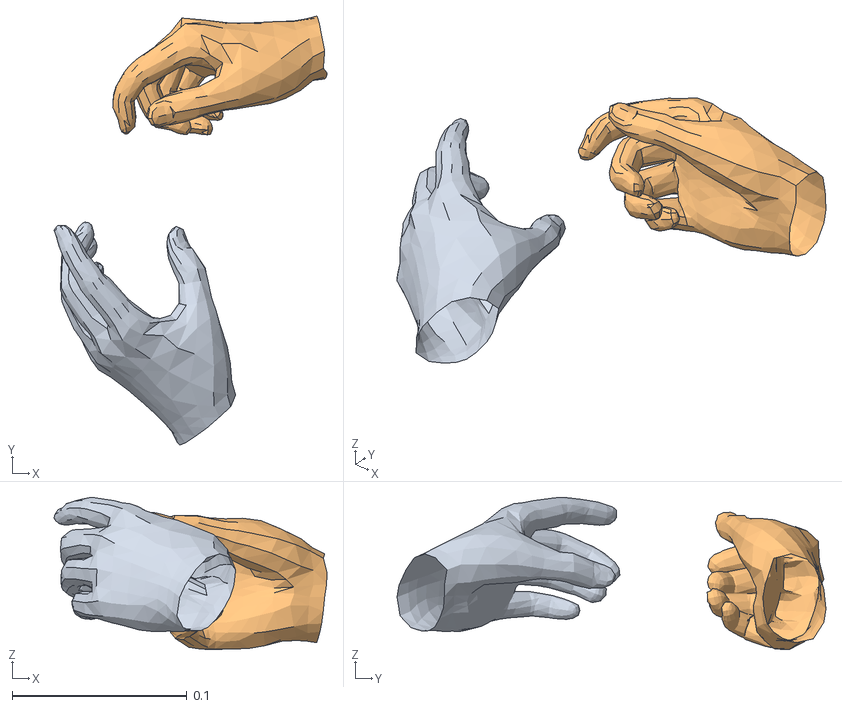
[picture p78: CAD file, 2026-04-30]
outputs/30th April 2026 - mesh sequence [20260430 manipulation]/mesh_0181.obj
0.156 x 0.246 x 0.0873
hand_slot0
hand_slot1
