kckanav/head-camera-cv/outputs/30th April 2026 - mesh sequence [20260430 manipulation]/mesh_0268.obj

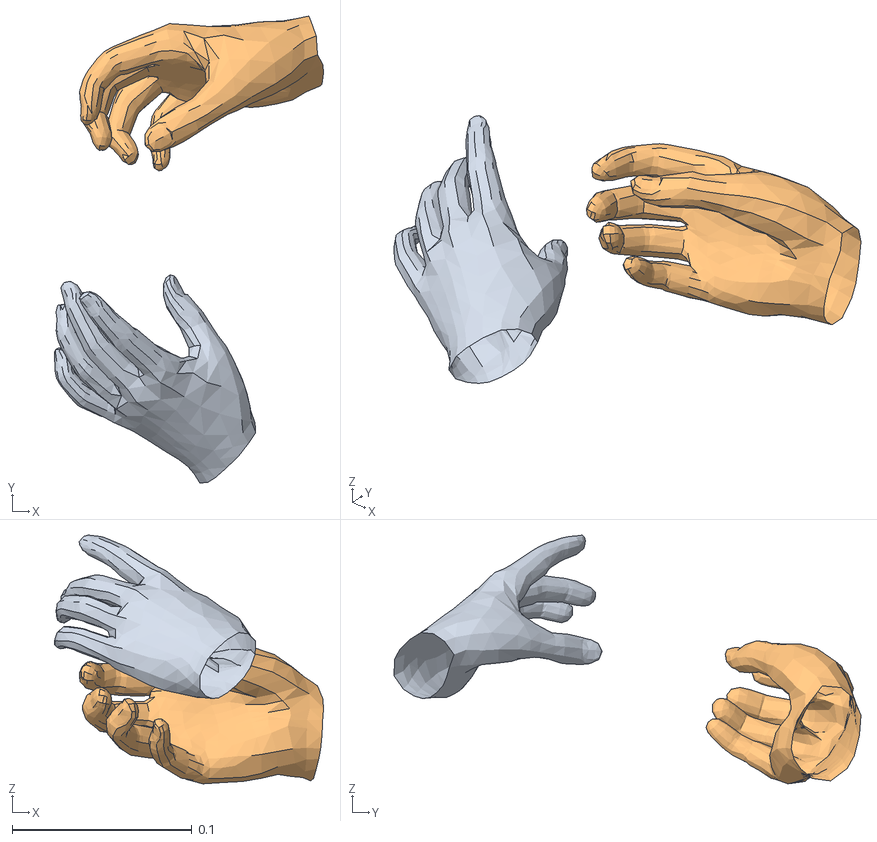
[picture p79: CAD file, 2026-04-30]
outputs/30th April 2026 - mesh sequence [20260430 manipulation]/mesh_0268.obj
0.15 x 0.26 x 0.139
hand_slot0
hand_slot1
