kckanav/head-camera-cv/outputs/30th April 2026 - mesh sequence [20260430 manipulation]/mesh_0281.obj

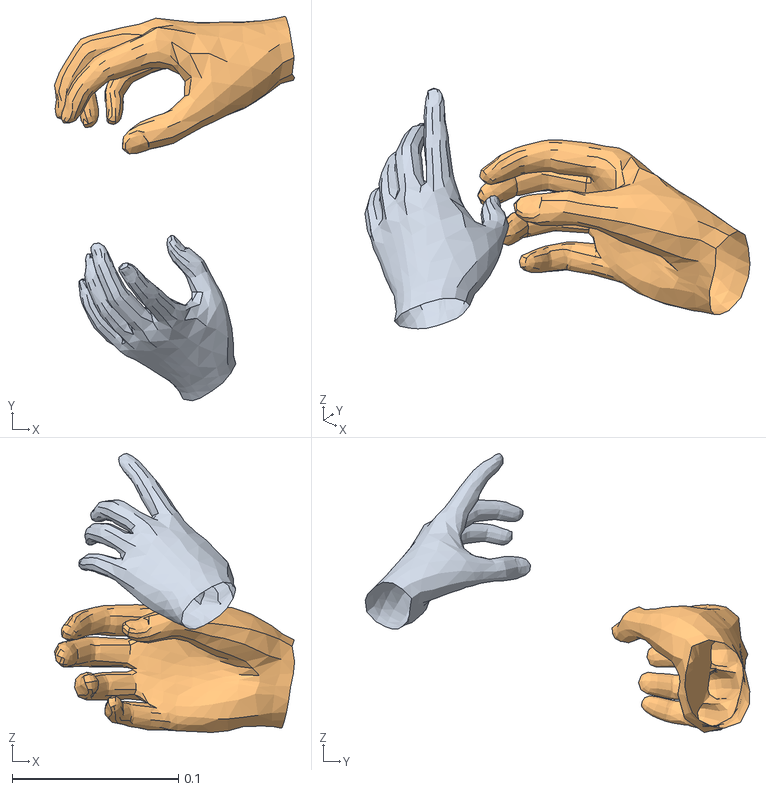
[picture p80: CAD file, 2026-04-30]
outputs/30th April 2026 - mesh sequence [20260430 manipulation]/mesh_0281.obj
0.145 x 0.232 x 0.168
hand_slot0
hand_slot1
