kckanav/head-camera-cv/outputs/30th April 2026 - mesh sequence [20260430 manipulation]/mesh_0053.obj

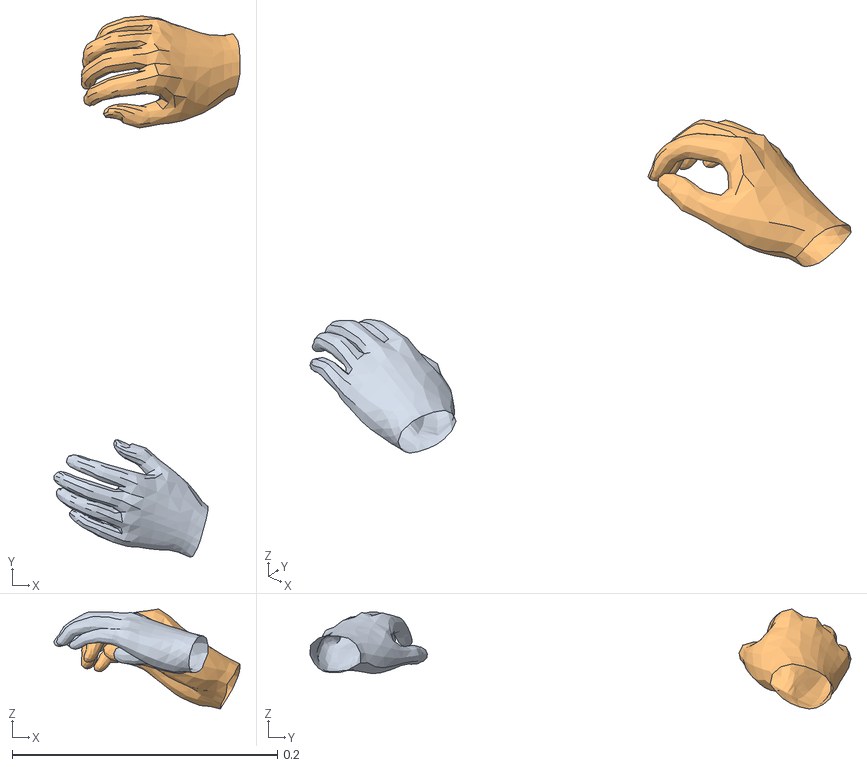
[picture p81: CAD file, 2026-04-30]
outputs/30th April 2026 - mesh sequence [20260430 manipulation]/mesh_0053.obj
0.14 x 0.408 x 0.0754
hand_slot0
hand_slot1
