kckanav/head-camera-cv/outputs/30th April 2026 - mesh sequence [20260430 manipulation]/mesh_0446.obj

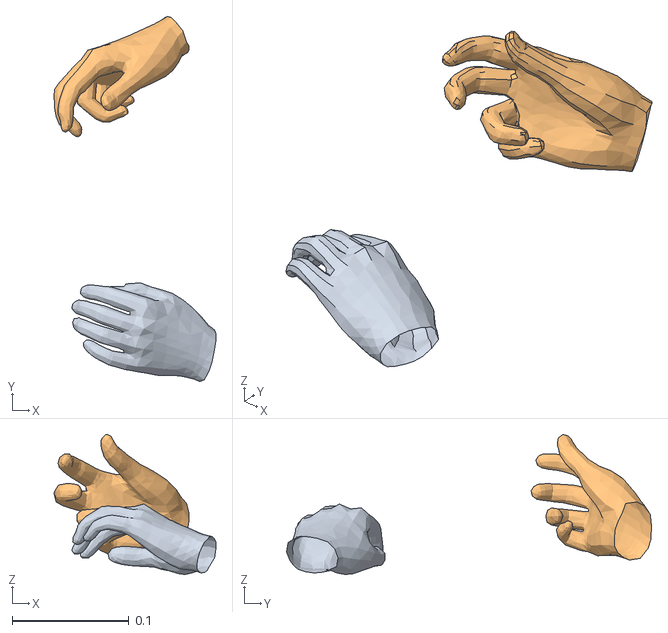
[picture p82: CAD file, 2026-04-30]
outputs/30th April 2026 - mesh sequence [20260430 manipulation]/mesh_0446.obj
0.138 x 0.312 x 0.12
hand_slot0
hand_slot1
