kckanav/head-camera-cv/outputs/30th April 2026 - mesh sequence [20260430 manipulation]/mesh_0394.obj

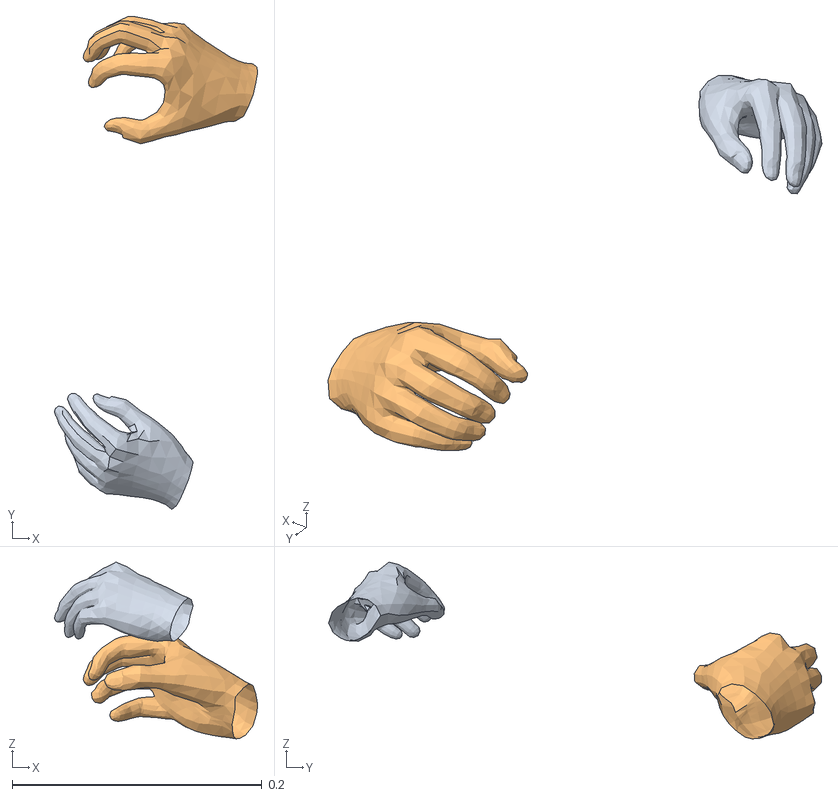
[picture p83: CAD file, 2026-04-30]
outputs/30th April 2026 - mesh sequence [20260430 manipulation]/mesh_0394.obj
0.163 x 0.395 x 0.142
hand_slot0
hand_slot1
