kckanav/head-camera-cv/outputs/30th April 2026 - mesh sequence [20260430 manipulation]/mesh_0247.obj

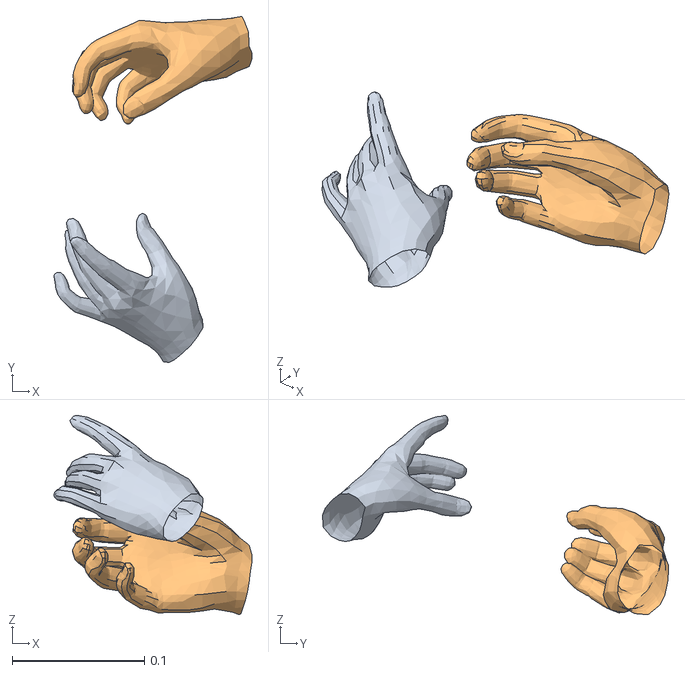
[picture p84: CAD file, 2026-04-30]
outputs/30th April 2026 - mesh sequence [20260430 manipulation]/mesh_0247.obj
0.149 x 0.261 x 0.151
hand_slot0
hand_slot1
