kckanav/head-camera-cv/outputs/30th April 2026 - mesh sequence [20260430 manipulation]/mesh_0399.obj

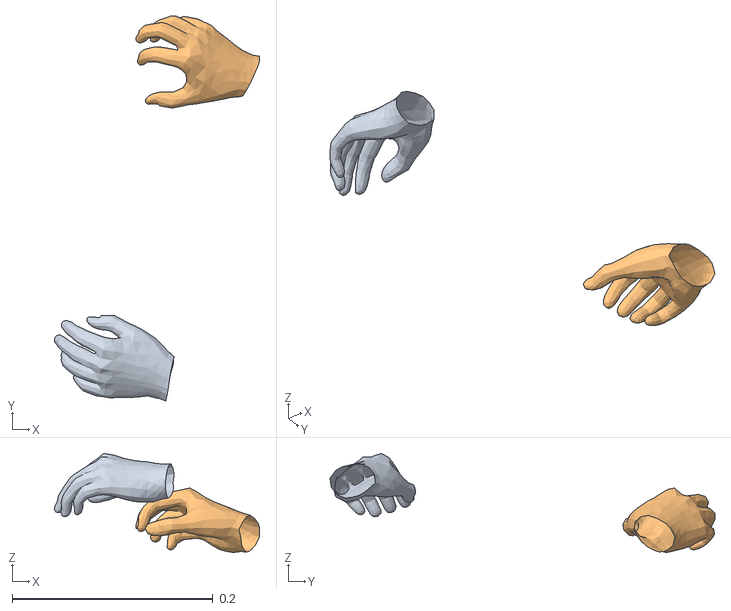
[picture p85: CAD file, 2026-04-30]
outputs/30th April 2026 - mesh sequence [20260430 manipulation]/mesh_0399.obj
0.205 x 0.384 x 0.0988
hand_slot0
hand_slot1
