kckanav/head-camera-cv/outputs/30th April 2026 - mesh sequence [20260430 manipulation]/mesh_0250.obj

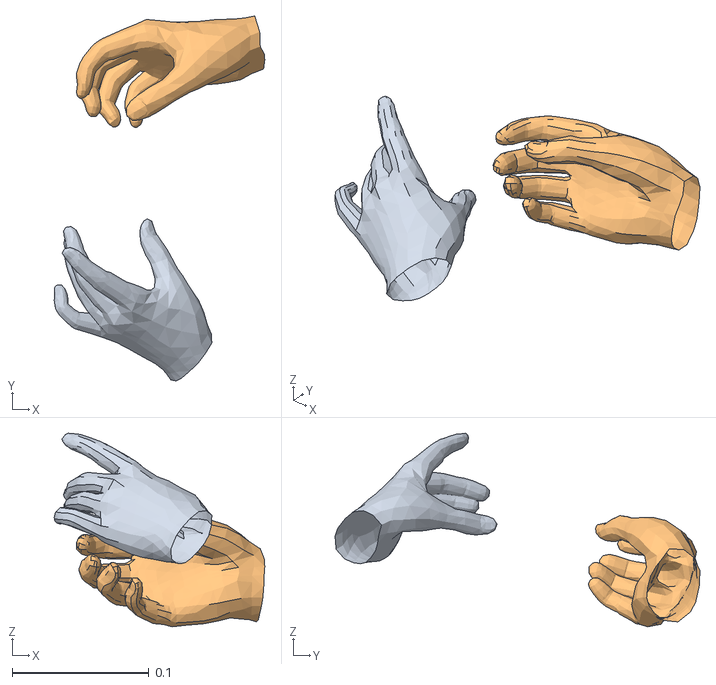
[picture p86: CAD file, 2026-04-30]
outputs/30th April 2026 - mesh sequence [20260430 manipulation]/mesh_0250.obj
0.154 x 0.267 x 0.142
hand_slot0
hand_slot1
