kckanav/head-camera-cv/outputs/30th April 2026 - mesh sequence [20260430 manipulation]/mesh_0124.obj

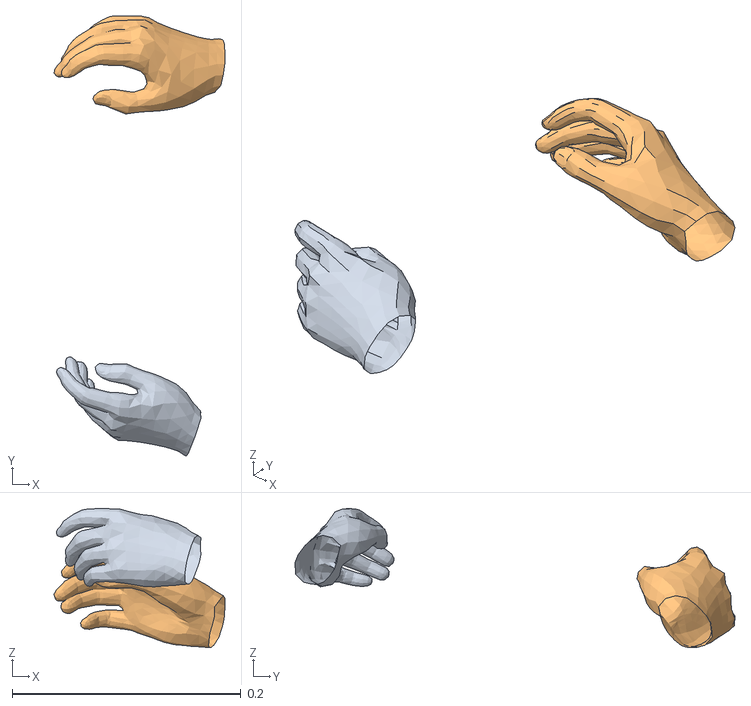
[picture p87: CAD file, 2026-04-30]
outputs/30th April 2026 - mesh sequence [20260430 manipulation]/mesh_0124.obj
0.149 x 0.385 x 0.122
hand_slot0
hand_slot1
