kckanav/head-camera-cv/outputs/30th April 2026 - mesh sequence [20260430 manipulation]/mesh_0037.obj

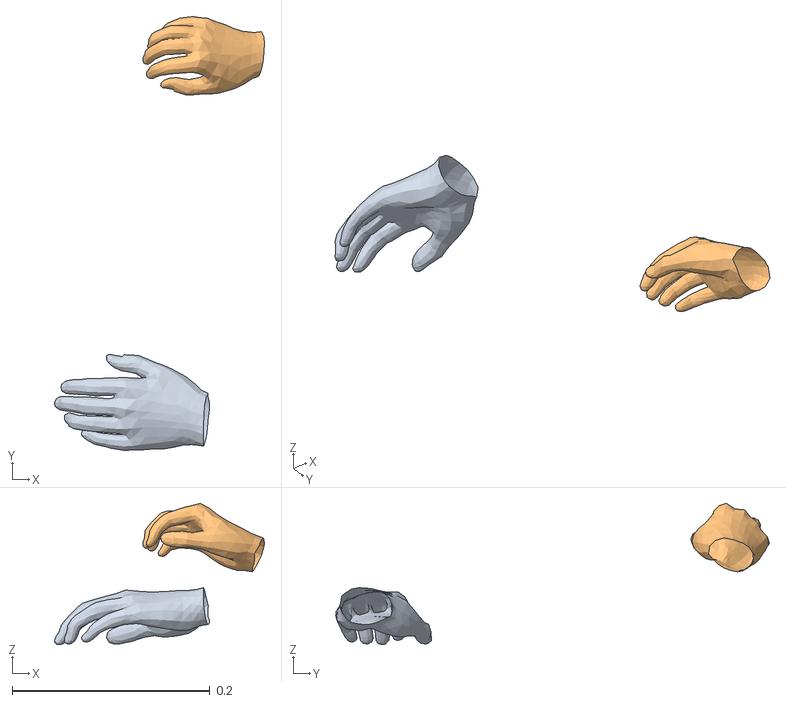
[picture p88: CAD file, 2026-04-30]
outputs/30th April 2026 - mesh sequence [20260430 manipulation]/mesh_0037.obj
0.213 x 0.439 x 0.143
hand_slot0
hand_slot1
