kckanav/head-camera-cv/outputs/30th April 2026 - mesh sequence [20260430 manipulation]/mesh_0063.obj

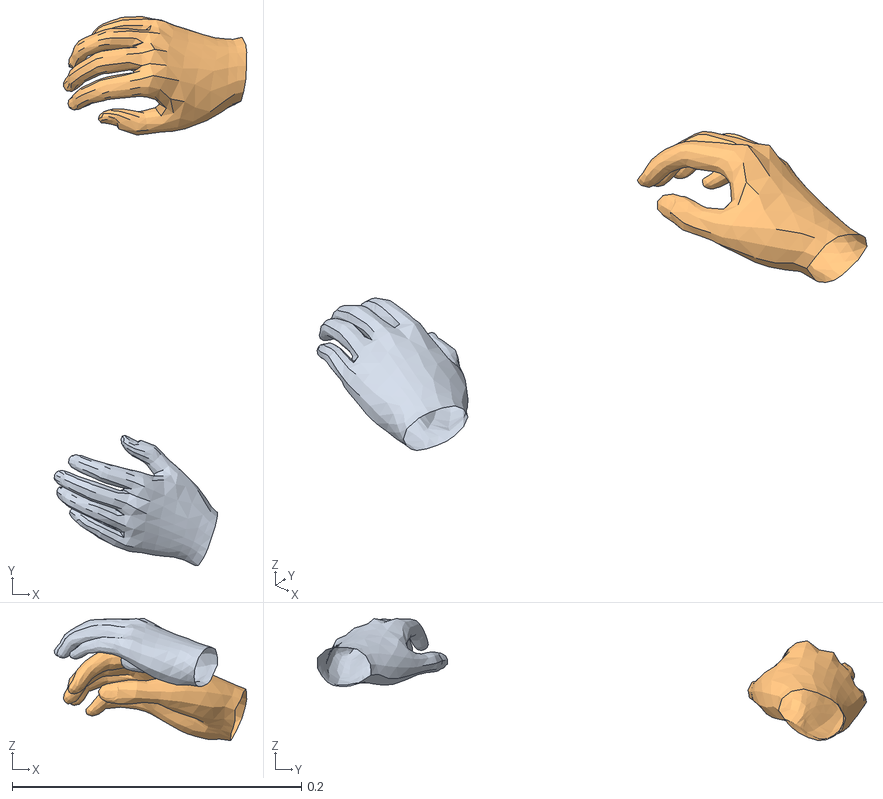
[picture p89: CAD file, 2026-04-30]
outputs/30th April 2026 - mesh sequence [20260430 manipulation]/mesh_0063.obj
0.133 x 0.38 x 0.0845
hand_slot0
hand_slot1
