kckanav/head-camera-cv/outputs/30th April 2026 - mesh sequence [20260430 manipulation]/mesh_0434.obj

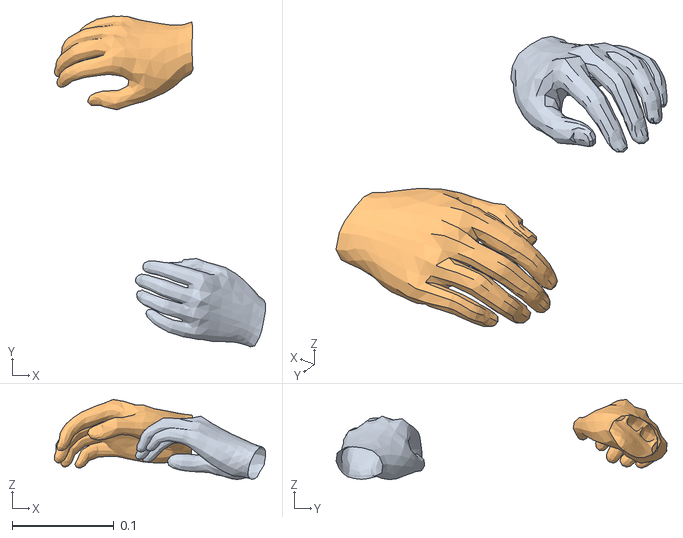
[picture p90: CAD file, 2026-04-30]
outputs/30th April 2026 - mesh sequence [20260430 manipulation]/mesh_0434.obj
0.208 x 0.326 x 0.079
hand_slot0
hand_slot1
