kckanav/head-camera-cv/outputs/30th April 2026 - mesh sequence [20260430 manipulation]/mesh_0175.obj

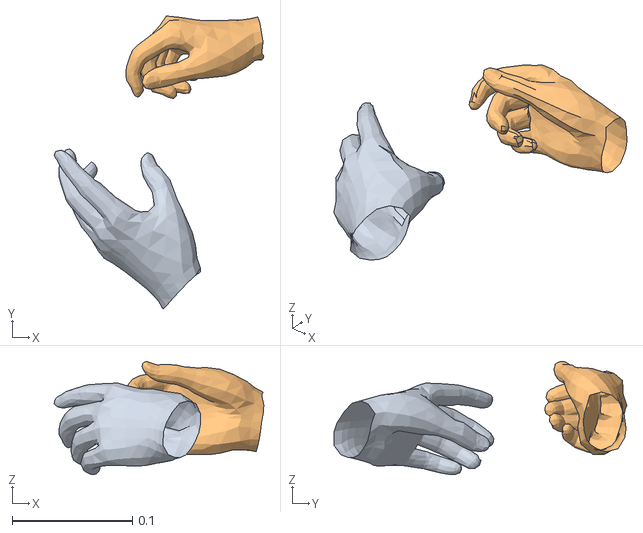
[picture p91: CAD file, 2026-04-30]
outputs/30th April 2026 - mesh sequence [20260430 manipulation]/mesh_0175.obj
0.174 x 0.243 x 0.094
hand_slot0
hand_slot1
