kckanav/head-camera-cv/outputs/30th April 2026 - mesh sequence [20260430 manipulation]/mesh_0439.obj

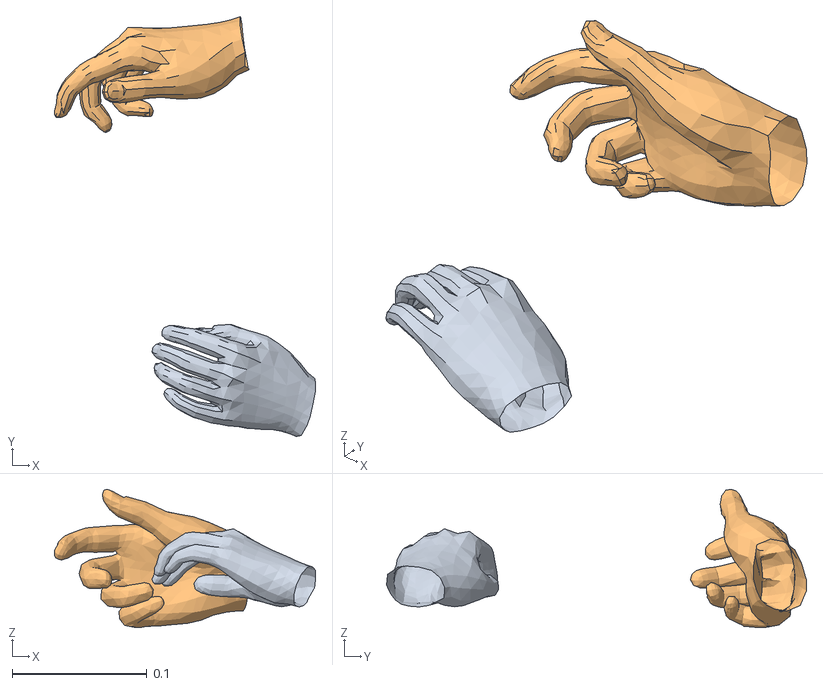
[picture p92: CAD file, 2026-04-30]
outputs/30th April 2026 - mesh sequence [20260430 manipulation]/mesh_0439.obj
0.194 x 0.312 x 0.103
hand_slot0
hand_slot1
