kckanav/head-camera-cv/outputs/30th April 2026 - mesh sequence [20260430 manipulation]/mesh_0054.obj

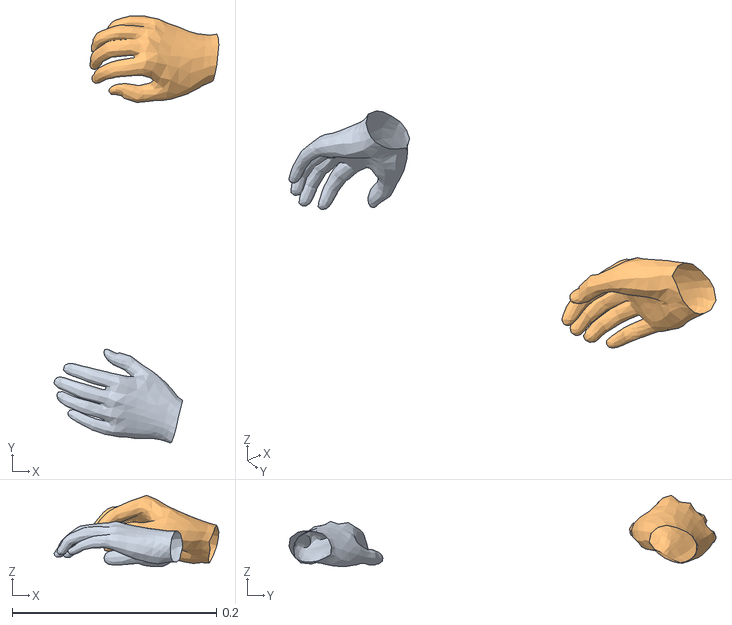
[picture p93: CAD file, 2026-04-30]
outputs/30th April 2026 - mesh sequence [20260430 manipulation]/mesh_0054.obj
0.161 x 0.418 x 0.0698
hand_slot0
hand_slot1
