kckanav/head-camera-cv/outputs/30th April 2026 - mesh sequence [20260430 manipulation]/mesh_0489.obj

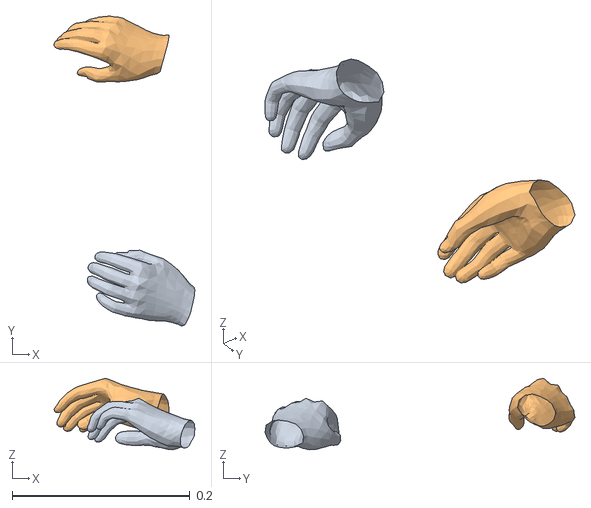
[picture p94: CAD file, 2026-04-30]
outputs/30th April 2026 - mesh sequence [20260430 manipulation]/mesh_0489.obj
0.158 x 0.349 x 0.0804
hand_slot0
hand_slot1
