kckanav/head-camera-cv/outputs/30th April 2026 - mesh sequence [20260430 manipulation]/mesh_0457.obj

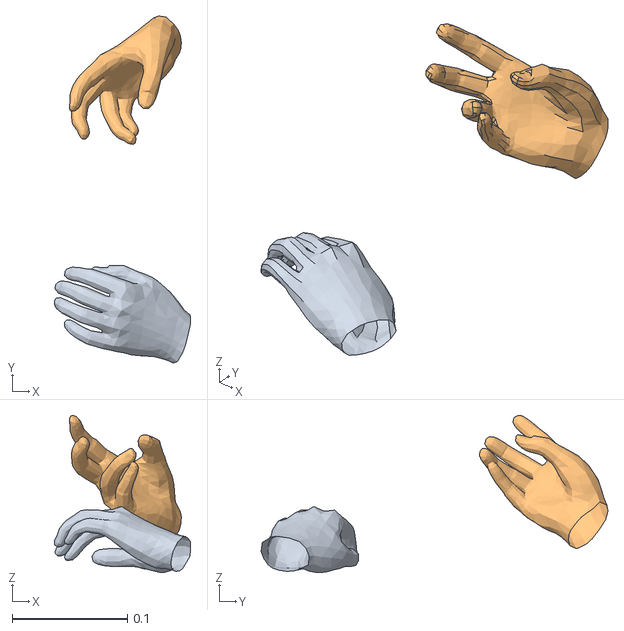
[picture p95: CAD file, 2026-04-30]
outputs/30th April 2026 - mesh sequence [20260430 manipulation]/mesh_0457.obj
0.118 x 0.301 x 0.136
hand_slot0
hand_slot1
