kckanav/head-camera-cv/outputs/30th April 2026 - mesh sequence [20260430 manipulation]/mesh_0029.obj

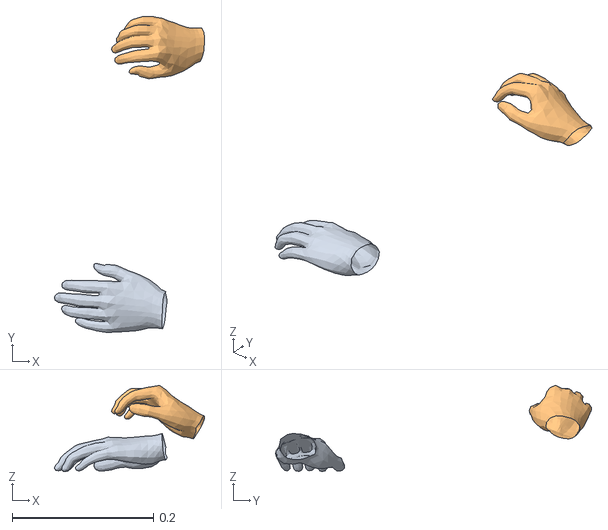
[picture p96: CAD file, 2026-04-30]
outputs/30th April 2026 - mesh sequence [20260430 manipulation]/mesh_0029.obj
0.213 x 0.448 x 0.122
hand_slot0
hand_slot1
