kckanav/head-camera-cv/outputs/30th April 2026 - mesh sequence [20260430 manipulation]/mesh_0373.obj

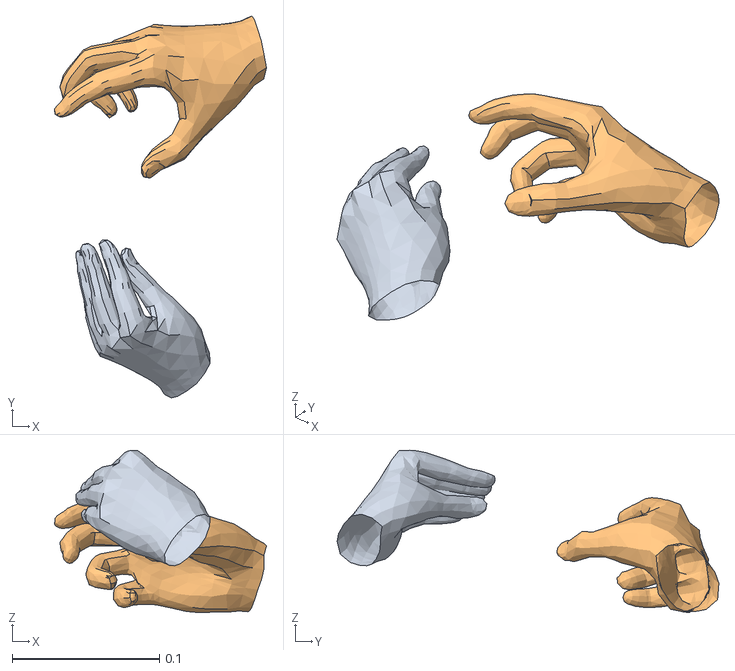
[picture p97: CAD file, 2026-04-30]
outputs/30th April 2026 - mesh sequence [20260430 manipulation]/mesh_0373.obj
0.144 x 0.259 x 0.11
hand_slot0
hand_slot1
