kckanav/head-camera-cv/outputs/30th April 2026 - mesh sequence [20260430 manipulation]/mesh_0363.obj

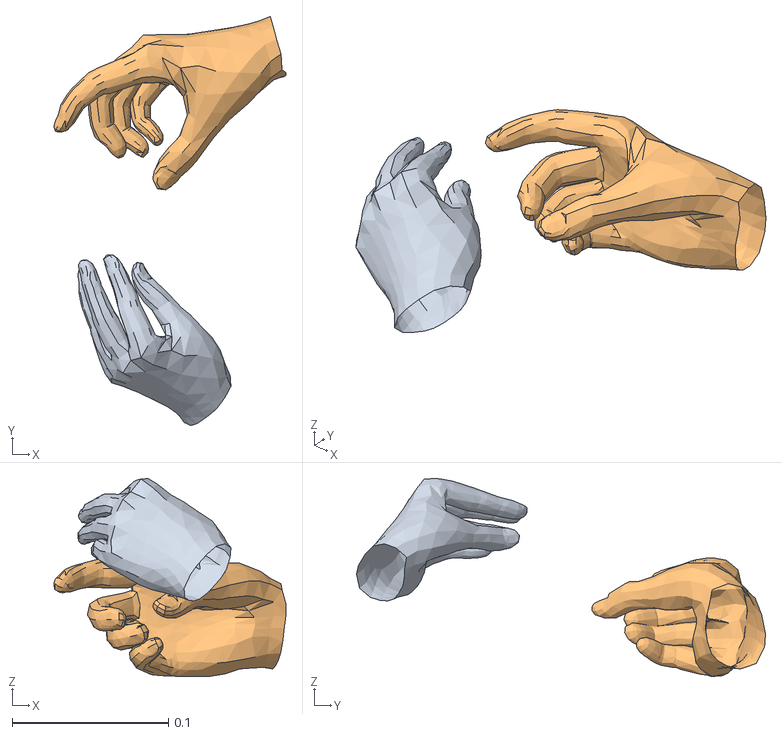
[picture p98: CAD file, 2026-04-30]
outputs/30th April 2026 - mesh sequence [20260430 manipulation]/mesh_0363.obj
0.148 x 0.261 x 0.127
hand_slot0
hand_slot1
