kckanav/head-camera-cv/outputs/30th April 2026 - mesh sequence [20260430 manipulation]/mesh_0126.obj

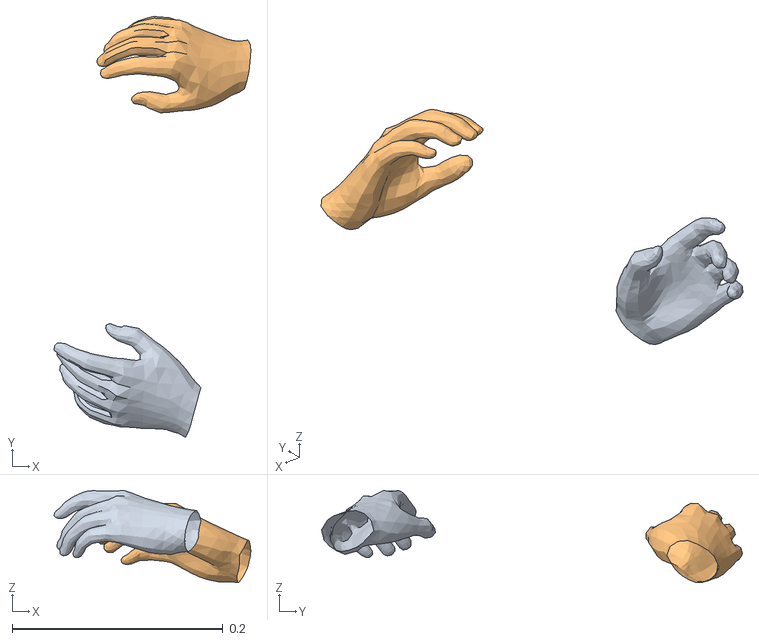
[picture p99: CAD file, 2026-04-30]
outputs/30th April 2026 - mesh sequence [20260430 manipulation]/mesh_0126.obj
0.187 x 0.399 x 0.0875
hand_slot0
hand_slot1
