kckanav/head-camera-cv/outputs/30th April 2026 - mesh sequence [20260430 manipulation]/mesh_0282.obj

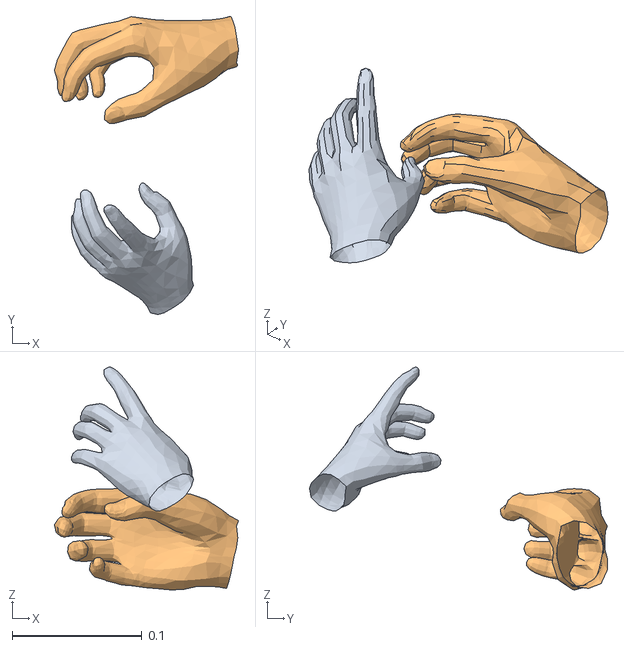
[picture p100: CAD file, 2026-04-30]
outputs/30th April 2026 - mesh sequence [20260430 manipulation]/mesh_0282.obj
0.142 x 0.23 x 0.172
hand_slot0
hand_slot1
