kckanav/head-camera-cv/outputs/30th April 2026 - mesh sequence [20260430 manipulation]/mesh_0428.obj

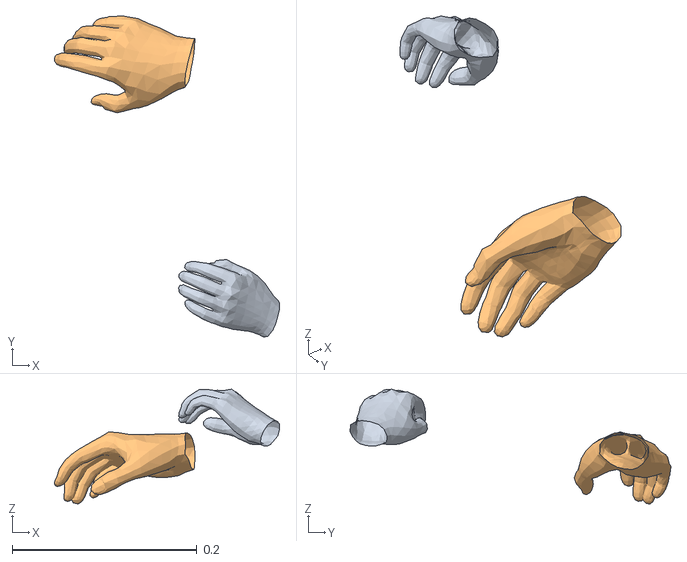
[picture p101: CAD file, 2026-04-30]
outputs/30th April 2026 - mesh sequence [20260430 manipulation]/mesh_0428.obj
0.244 x 0.348 x 0.124
hand_slot0
hand_slot1
