kckanav/head-camera-cv/outputs/30th April 2026 - mesh sequence [20260430 manipulation]/mesh_0206.obj

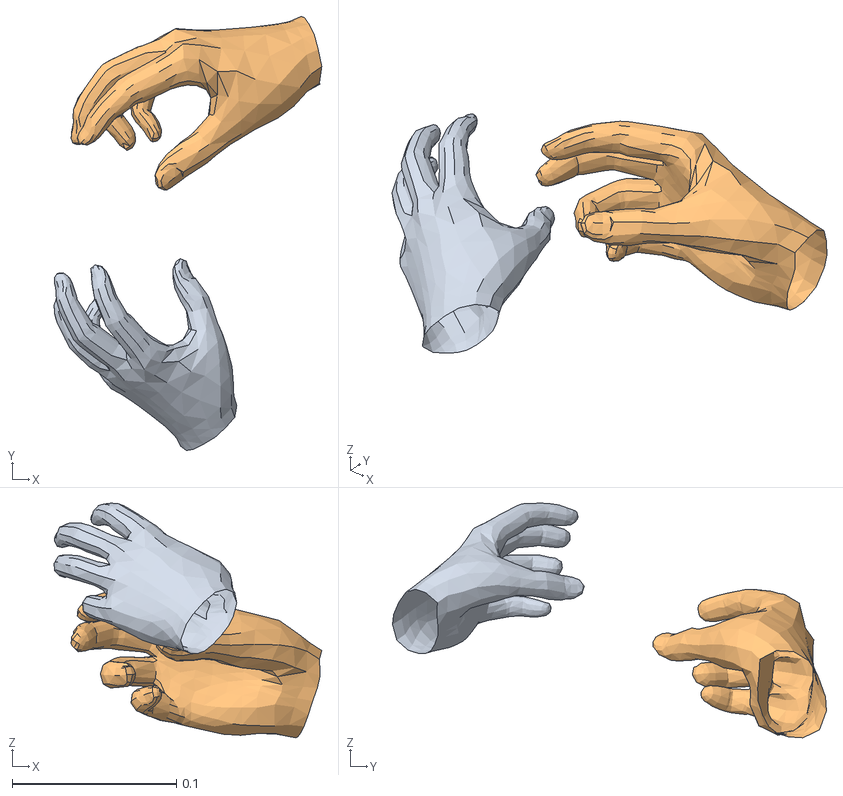
[picture p102: CAD file, 2026-04-30]
outputs/30th April 2026 - mesh sequence [20260430 manipulation]/mesh_0206.obj
0.163 x 0.264 x 0.143
hand_slot0
hand_slot1
