kckanav/head-camera-cv/outputs/30th April 2026 - mesh sequence [20260430 manipulation]/mesh_0513.obj

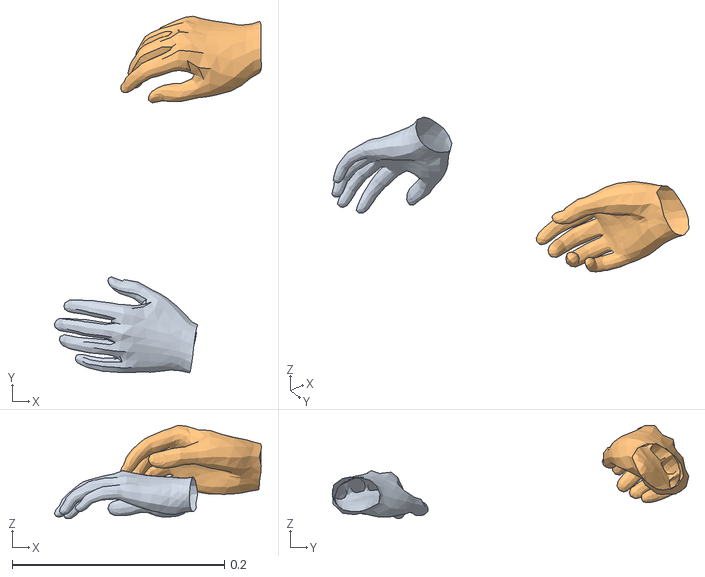
[picture p103: CAD file, 2026-04-30]
outputs/30th April 2026 - mesh sequence [20260430 manipulation]/mesh_0513.obj
0.195 x 0.336 x 0.088
hand_slot0
hand_slot1
