kckanav/head-camera-cv/outputs/30th April 2026 - mesh sequence [20260430 manipulation]/mesh_0046.obj

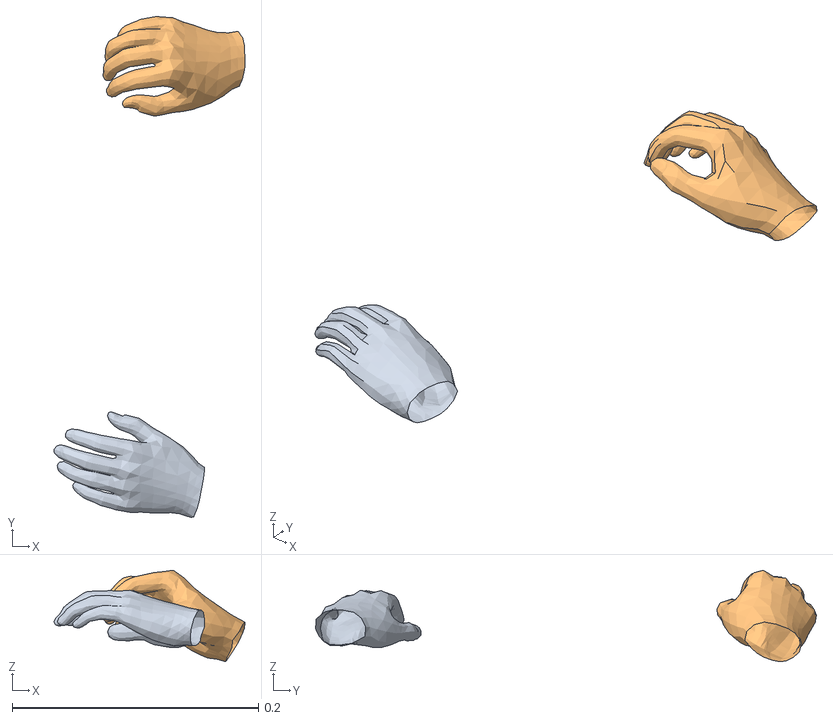
[picture p104: CAD file, 2026-04-30]
outputs/30th April 2026 - mesh sequence [20260430 manipulation]/mesh_0046.obj
0.155 x 0.407 x 0.0744
hand_slot0
hand_slot1
