kckanav/head-camera-cv/outputs/30th April 2026 - mesh sequence [20260430 manipulation]/mesh_0086.obj

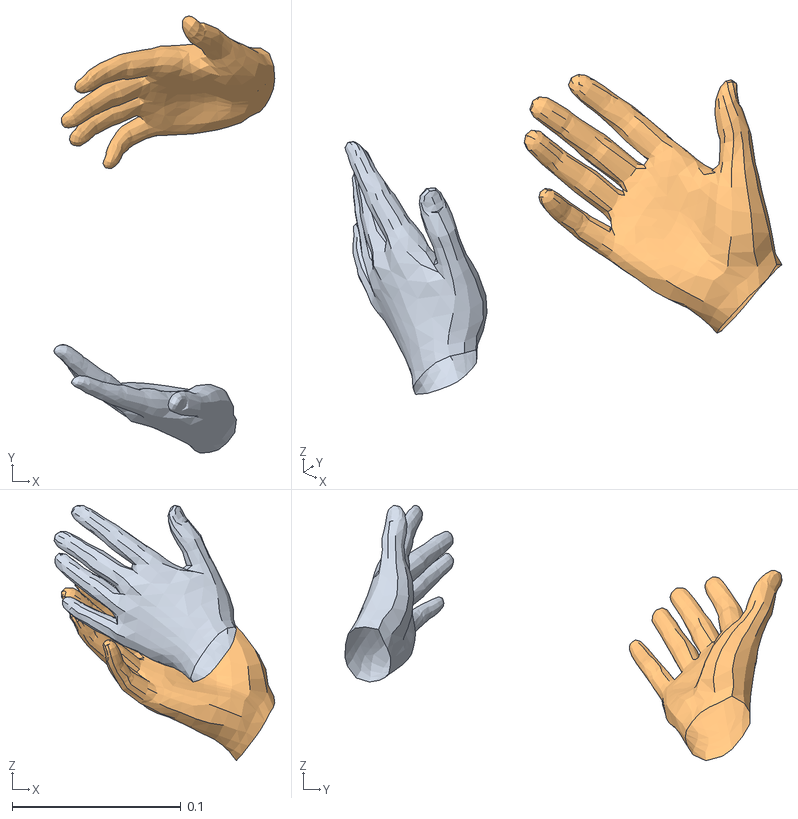
[picture p105: CAD file, 2026-04-30]
outputs/30th April 2026 - mesh sequence [20260430 manipulation]/mesh_0086.obj
0.131 x 0.259 x 0.151
hand_slot0
hand_slot1
