kckanav/head-camera-cv/outputs/30th April 2026 - mesh sequence [20260430 manipulation]/mesh_0308.obj

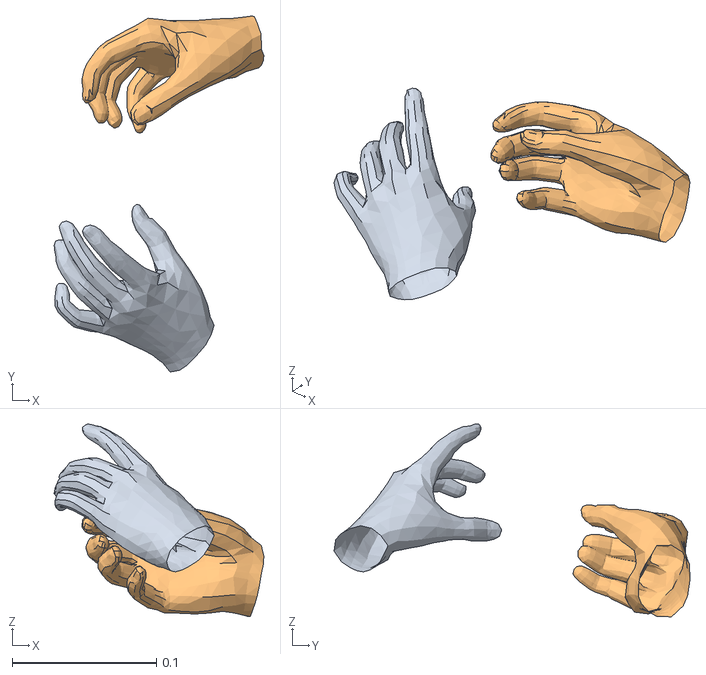
[picture p106: CAD file, 2026-04-30]
outputs/30th April 2026 - mesh sequence [20260430 manipulation]/mesh_0308.obj
0.146 x 0.247 x 0.134
hand_slot0
hand_slot1
