kckanav/head-camera-cv/outputs/30th April 2026 - mesh sequence [20260430 manipulation]/mesh_0383.obj

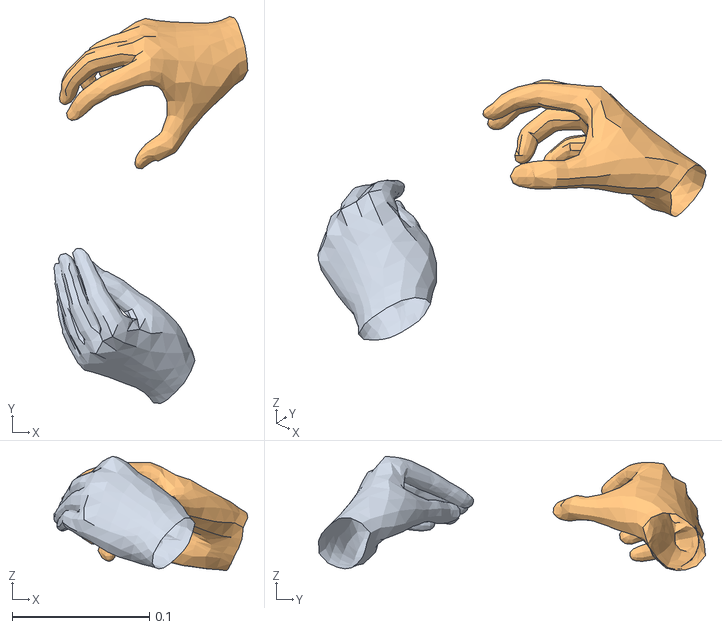
[picture p107: CAD file, 2026-04-30]
outputs/30th April 2026 - mesh sequence [20260430 manipulation]/mesh_0383.obj
0.141 x 0.282 x 0.0832
hand_slot0
hand_slot1
