kckanav/head-camera-cv/outputs/30th April 2026 - mesh sequence [20260430 manipulation]/mesh_0153.obj

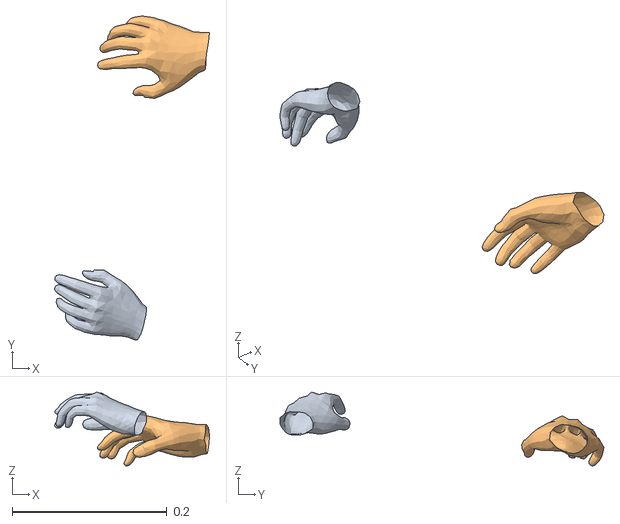
[picture p108: CAD file, 2026-04-30]
outputs/30th April 2026 - mesh sequence [20260430 manipulation]/mesh_0153.obj
0.2 x 0.419 x 0.0955
hand_slot0
hand_slot1
