kckanav/head-camera-cv/outputs/30th April 2026 - mesh sequence [20260430 manipulation]/mesh_0157.obj

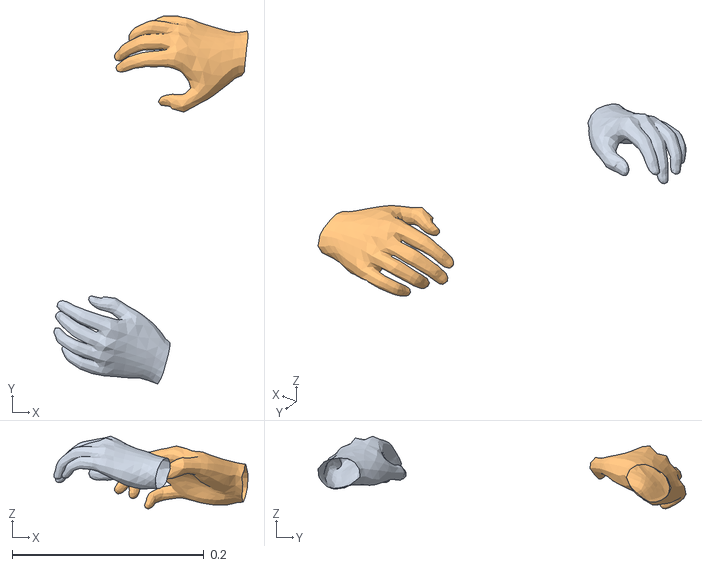
[picture p109: CAD file, 2026-04-30]
outputs/30th April 2026 - mesh sequence [20260430 manipulation]/mesh_0157.obj
0.202 x 0.383 x 0.0756
hand_slot0
hand_slot1
