kckanav/head-camera-cv/outputs/30th April 2026 - mesh sequence [20260430 manipulation]/mesh_0062.obj

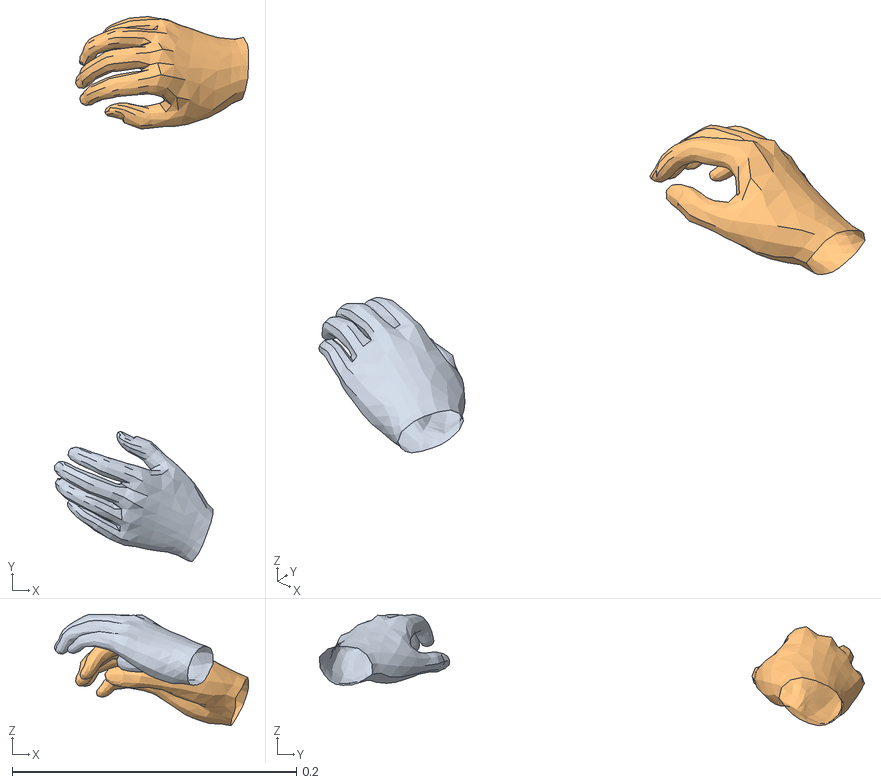
[picture p110: CAD file, 2026-04-30]
outputs/30th April 2026 - mesh sequence [20260430 manipulation]/mesh_0062.obj
0.137 x 0.384 x 0.0784
hand_slot0
hand_slot1
