kckanav/head-camera-cv/outputs/30th April 2026 - mesh sequence [20260430 manipulation]/mesh_0265.obj

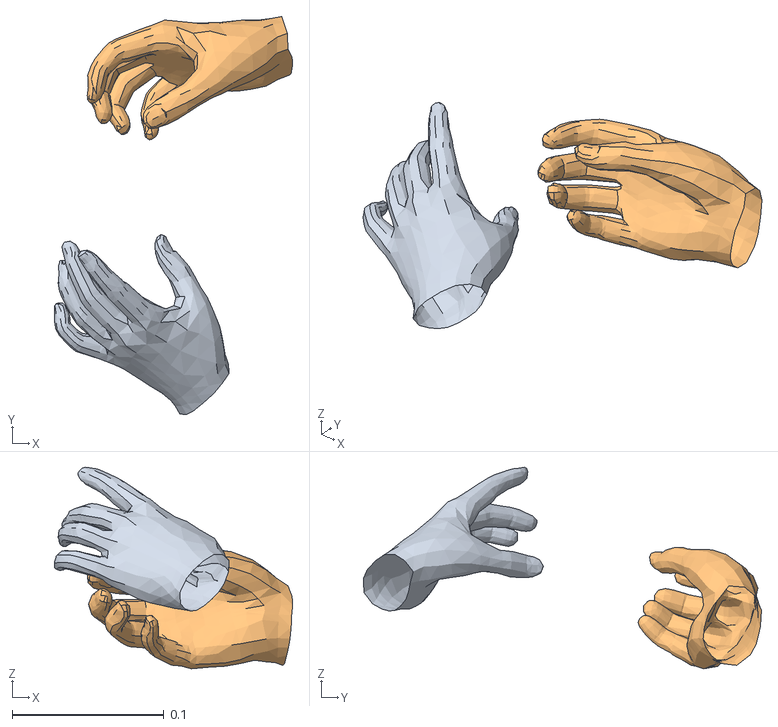
[picture p111: CAD file, 2026-04-30]
outputs/30th April 2026 - mesh sequence [20260430 manipulation]/mesh_0265.obj
0.157 x 0.262 x 0.133
hand_slot0
hand_slot1
