kckanav/head-camera-cv/outputs/30th April 2026 - mesh sequence [20260430 manipulation]/mesh_0314.obj

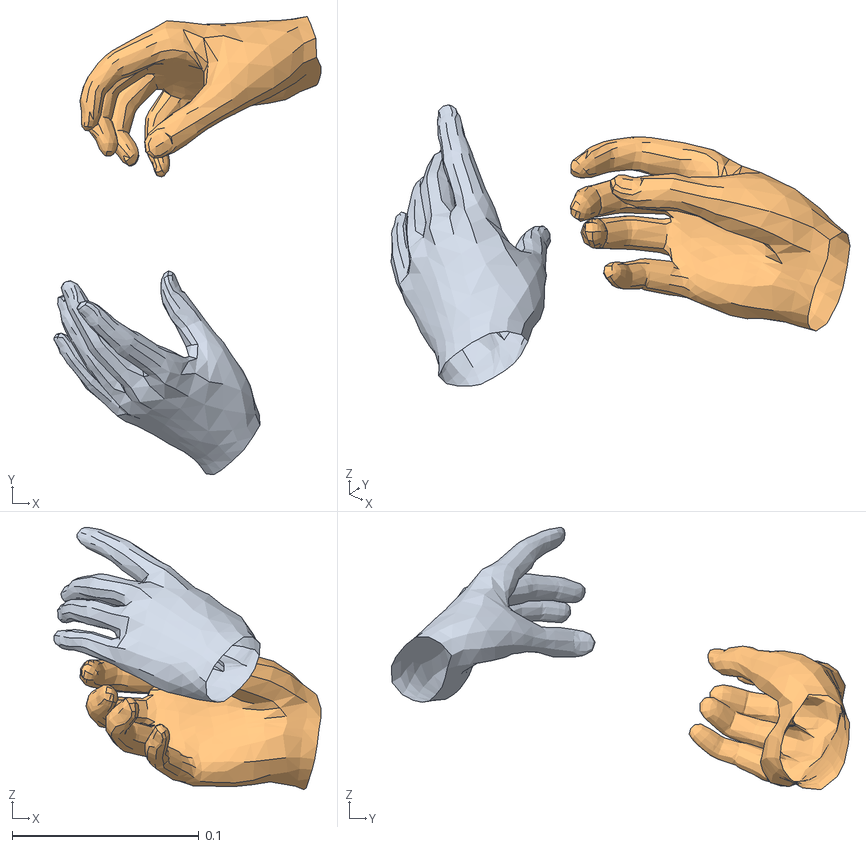
[picture p112: CAD file, 2026-04-30]
outputs/30th April 2026 - mesh sequence [20260430 manipulation]/mesh_0314.obj
0.143 x 0.245 x 0.14
hand_slot0
hand_slot1
