kckanav/head-camera-cv/outputs/30th April 2026 - mesh sequence [20260430 manipulation]/mesh_0430.obj

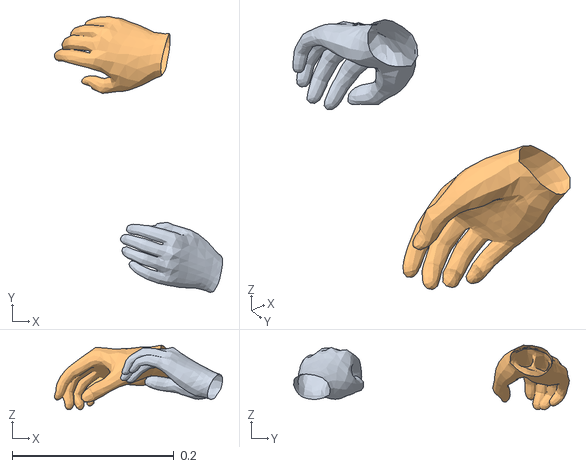
[picture p113: CAD file, 2026-04-30]
outputs/30th April 2026 - mesh sequence [20260430 manipulation]/mesh_0430.obj
0.208 x 0.341 x 0.0798
hand_slot0
hand_slot1
