kckanav/head-camera-cv/outputs/30th April 2026 - mesh sequence [20260430 manipulation]/mesh_0164.obj

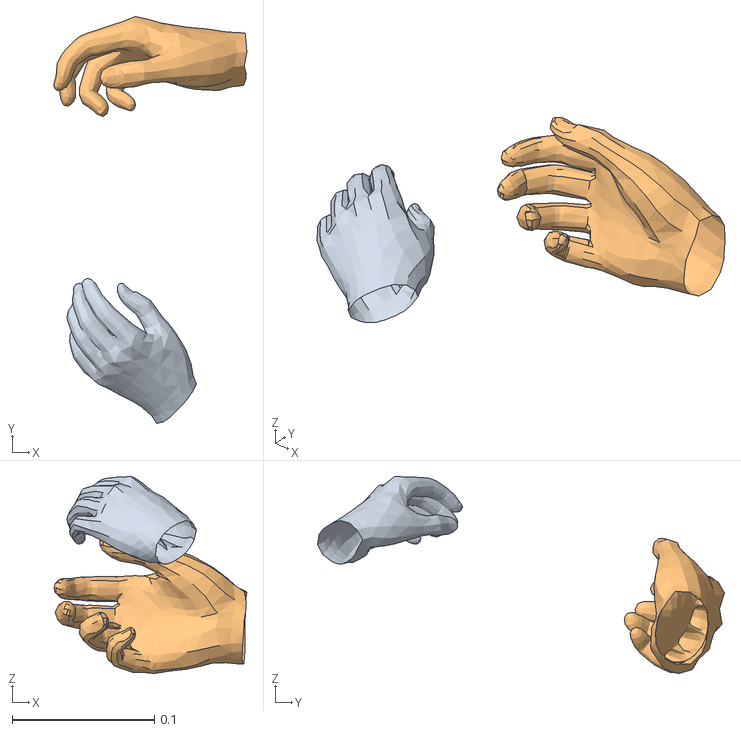
[picture p114: CAD file, 2026-04-30]
outputs/30th April 2026 - mesh sequence [20260430 manipulation]/mesh_0164.obj
0.136 x 0.286 x 0.139
hand_slot0
hand_slot1
