kckanav/head-camera-cv/outputs/30th April 2026 - mesh sequence [20260430 manipulation]/mesh_0143.obj

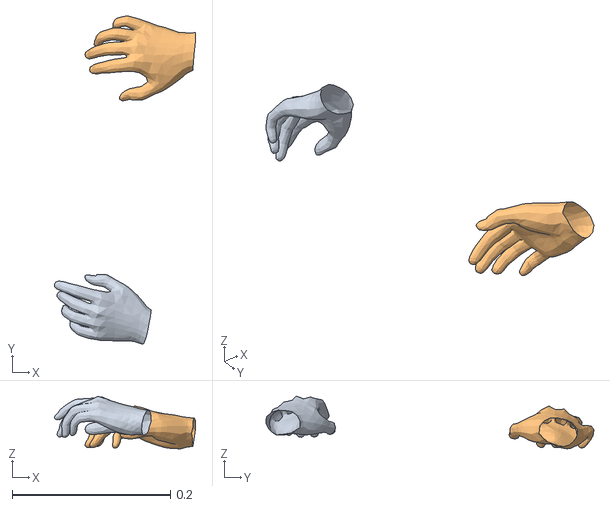
[picture p115: CAD file, 2026-04-30]
outputs/30th April 2026 - mesh sequence [20260430 manipulation]/mesh_0143.obj
0.179 x 0.415 x 0.0666
hand_slot0
hand_slot1
