kckanav/head-camera-cv/outputs/30th April 2026 - mesh sequence [20260430 manipulation]/mesh_0221.obj

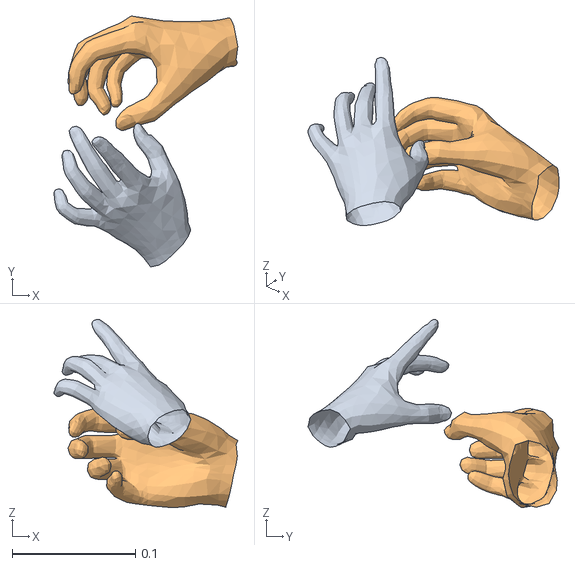
[picture p116: CAD file, 2026-04-30]
outputs/30th April 2026 - mesh sequence [20260430 manipulation]/mesh_0221.obj
0.149 x 0.203 x 0.153
hand_slot0
hand_slot1
