kckanav/head-camera-cv/outputs/30th April 2026 - mesh sequence [20260430 manipulation]/mesh_0060.obj

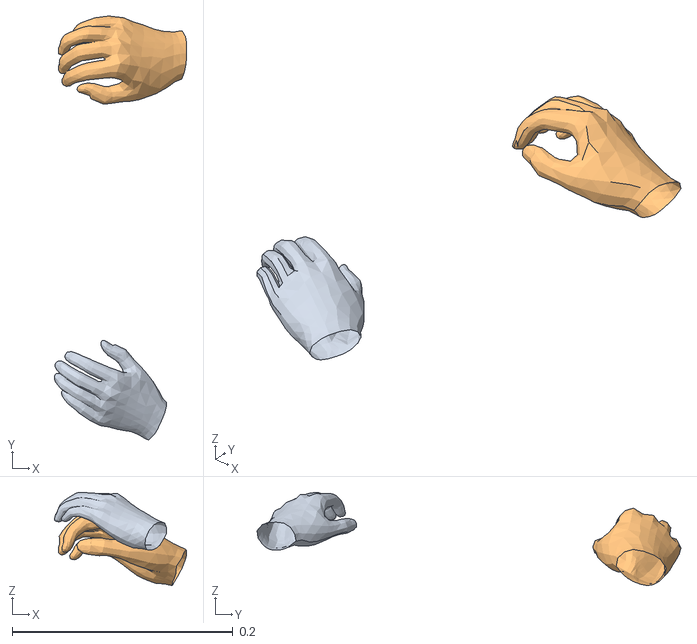
[picture p117: CAD file, 2026-04-30]
outputs/30th April 2026 - mesh sequence [20260430 manipulation]/mesh_0060.obj
0.12 x 0.384 x 0.0844
hand_slot0
hand_slot1
