kckanav/head-camera-cv/outputs/30th April 2026 - mesh sequence [20260430 manipulation]/mesh_0367.obj

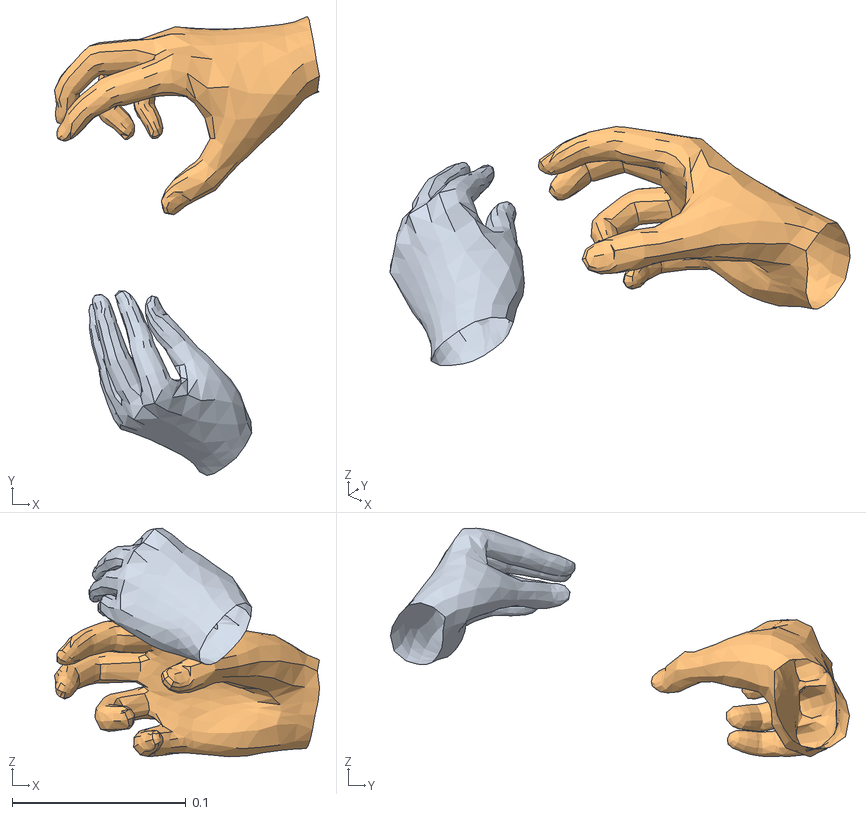
[picture p118: CAD file, 2026-04-30]
outputs/30th April 2026 - mesh sequence [20260430 manipulation]/mesh_0367.obj
0.153 x 0.264 x 0.132
hand_slot0
hand_slot1
