kckanav/head-camera-cv/outputs/30th April 2026 - mesh sequence [20260430 manipulation]/mesh_0280.obj

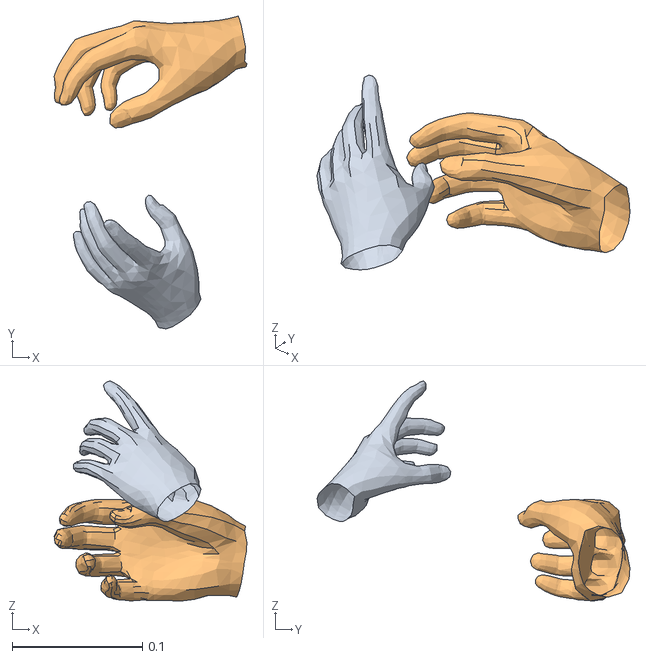
[picture p119: CAD file, 2026-04-30]
outputs/30th April 2026 - mesh sequence [20260430 manipulation]/mesh_0280.obj
0.148 x 0.24 x 0.169
hand_slot0
hand_slot1
