kckanav/head-camera-cv/outputs/30th April 2026 - mesh sequence [20260430 manipulation]/mesh_0186.obj

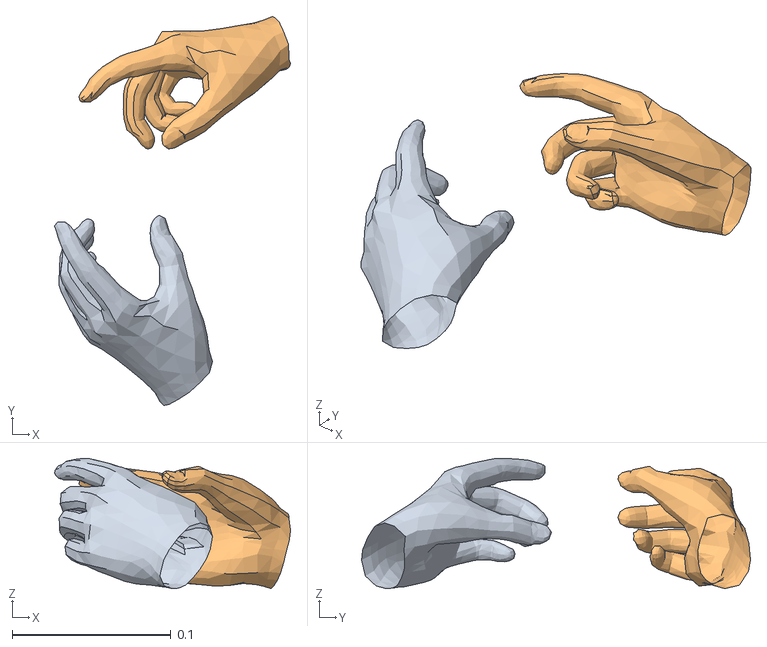
[picture p120: CAD file, 2026-04-30]
outputs/30th April 2026 - mesh sequence [20260430 manipulation]/mesh_0186.obj
0.149 x 0.245 x 0.082
hand_slot0
hand_slot1
