kckanav/head-camera-cv/outputs/30th April 2026 - mesh sequence [20260430 manipulation]/mesh_0244.obj

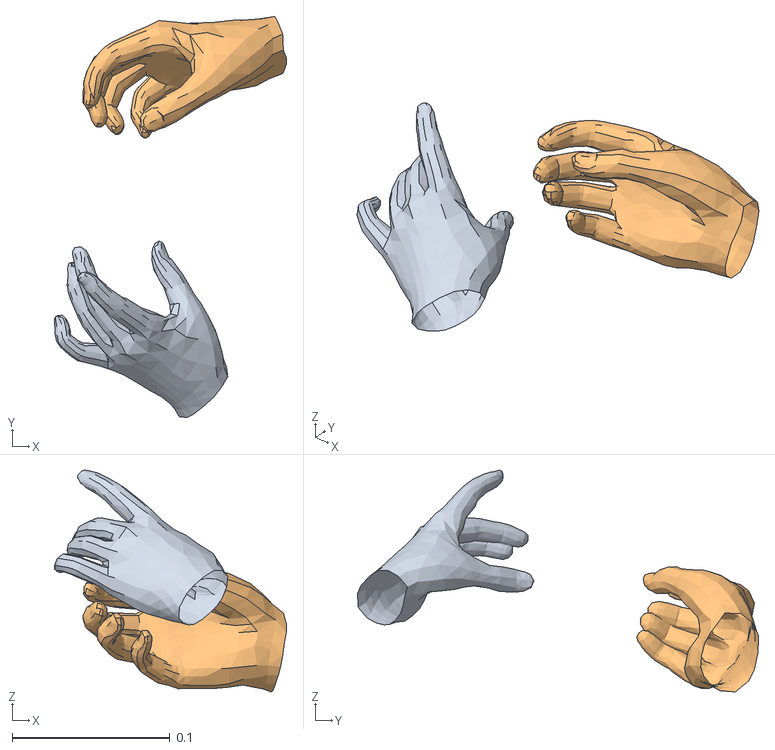
[picture p121: CAD file, 2026-04-30]
outputs/30th April 2026 - mesh sequence [20260430 manipulation]/mesh_0244.obj
0.147 x 0.255 x 0.141
hand_slot0
hand_slot1
