kckanav/head-camera-cv/outputs/30th April 2026 - mesh sequence [20260430 manipulation]/mesh_0484.obj

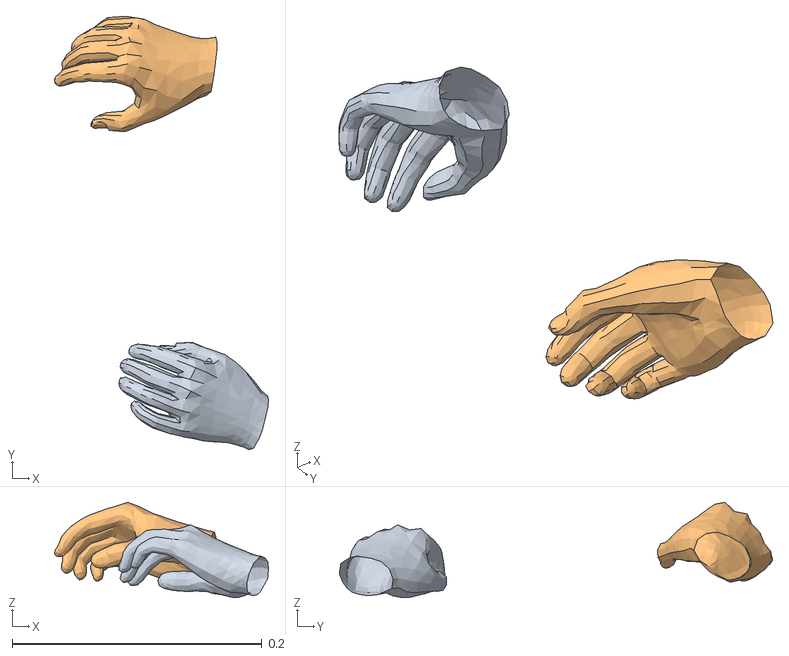
[picture p122: CAD file, 2026-04-30]
outputs/30th April 2026 - mesh sequence [20260430 manipulation]/mesh_0484.obj
0.171 x 0.347 x 0.0763
hand_slot0
hand_slot1
